ns8483/MAE156A_RobotAssistantCardiologist/Data/LinTrans.png

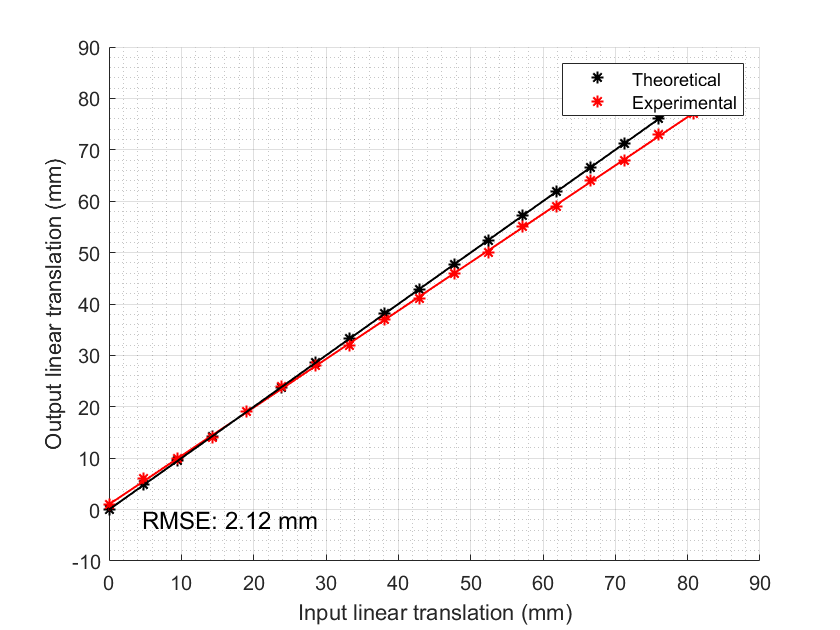
Data/LinTrans.png
