ns8483/MAE156A_RobotAssistantCardiologist/Data/Rot.png

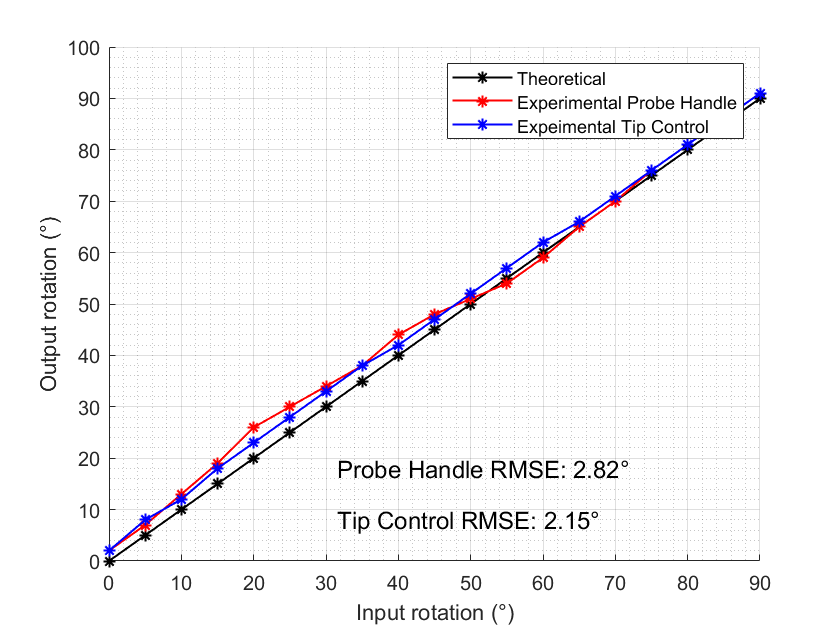
Data/Rot.png
