ns8483/MAE156A_RobotAssistantCardiologist/Images/Code Example.png

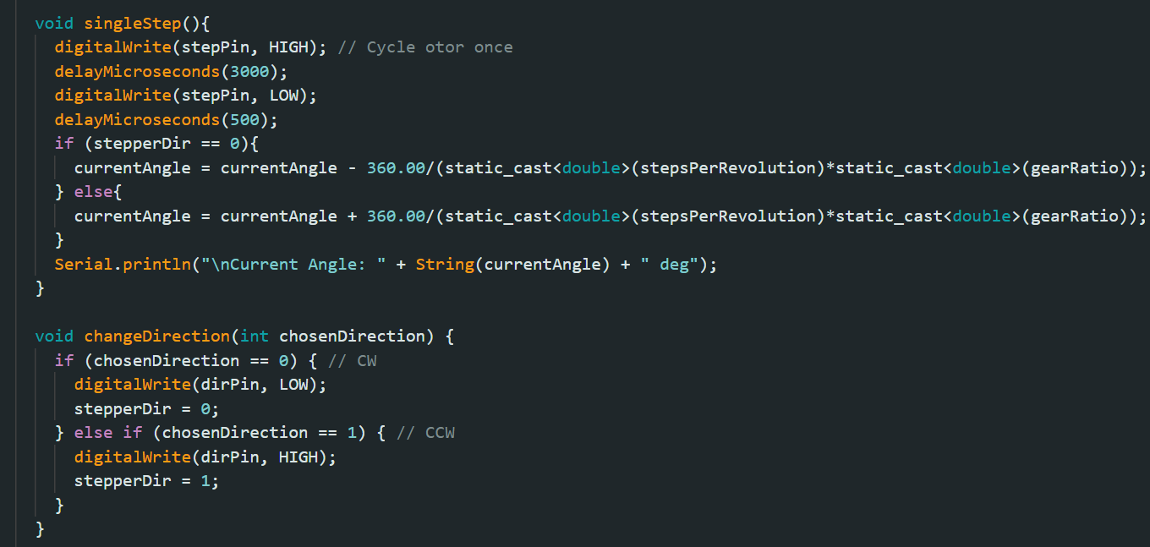
Images/Code Example.png
