ns8483/MAE156A_RobotAssistantCardiologist/Images/probe Image.png

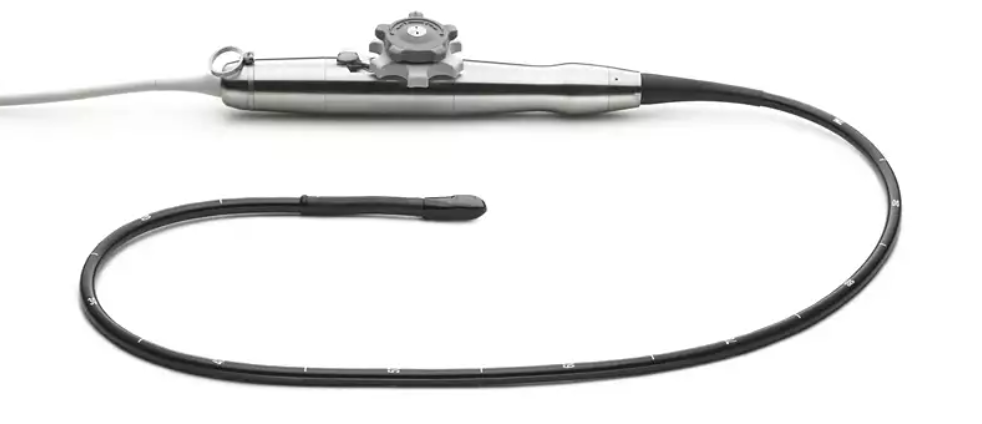
Images/probe Image.png
