ns8483/MAE156A_RobotAssistantCardiologist/Images/probe_housing.png

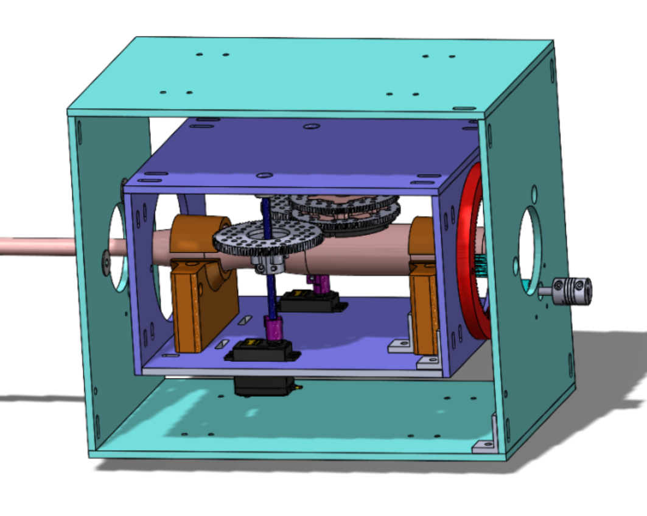
Images/probe_housing.png
