ns8483/MAE156A_RobotAssistantCardiologist/CAD/knob engagement, motorized rotation, passive translation/Inner Bearing Mount.SLDPRT

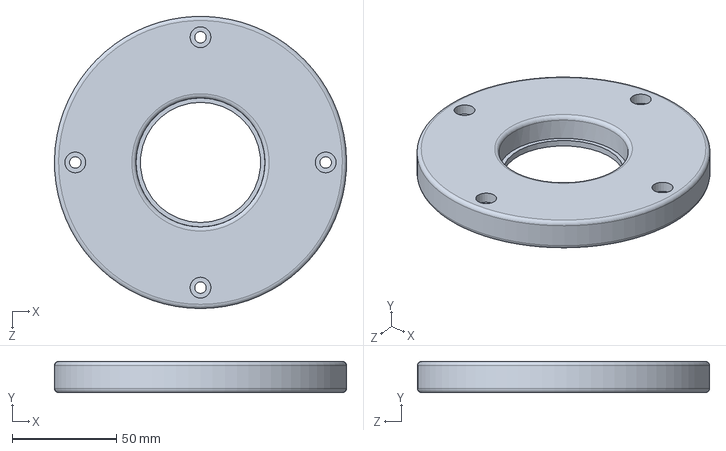
[picture p29: CAD file, 2024-04-29]
CAD/knob engagement, motorized rotation, passive translation/Inner Bearing Mount.SLDPRT
140.0 x 15.0 x 139.9 mm
