ns8483/MAE156A_RobotAssistantCardiologist/CAD/Probe and Housing/Hinge 2.SLDPRT

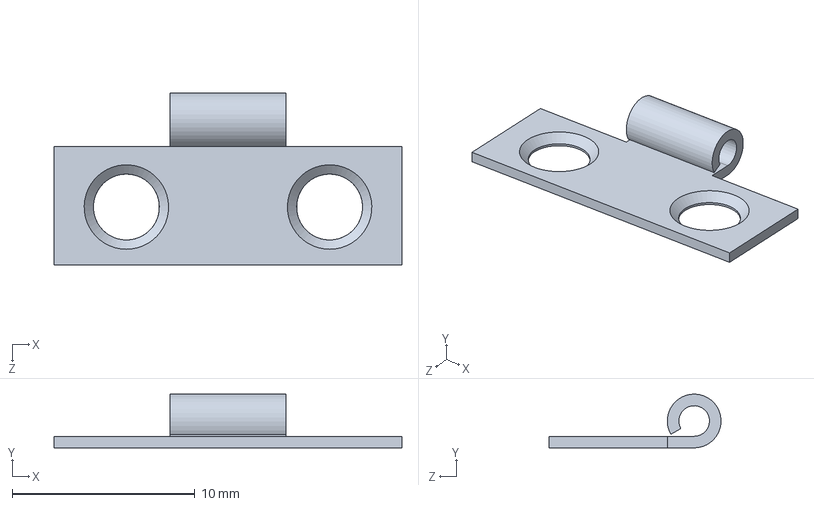
[picture p30: CAD file, 2024-04-26]
CAD/Probe and Housing/Hinge 2.SLDPRT
19.1 x 2.95 x 9.42 mm
