ns8483/MAE156A_RobotAssistantCardiologist/CAD/Base/Side.SLDPRT

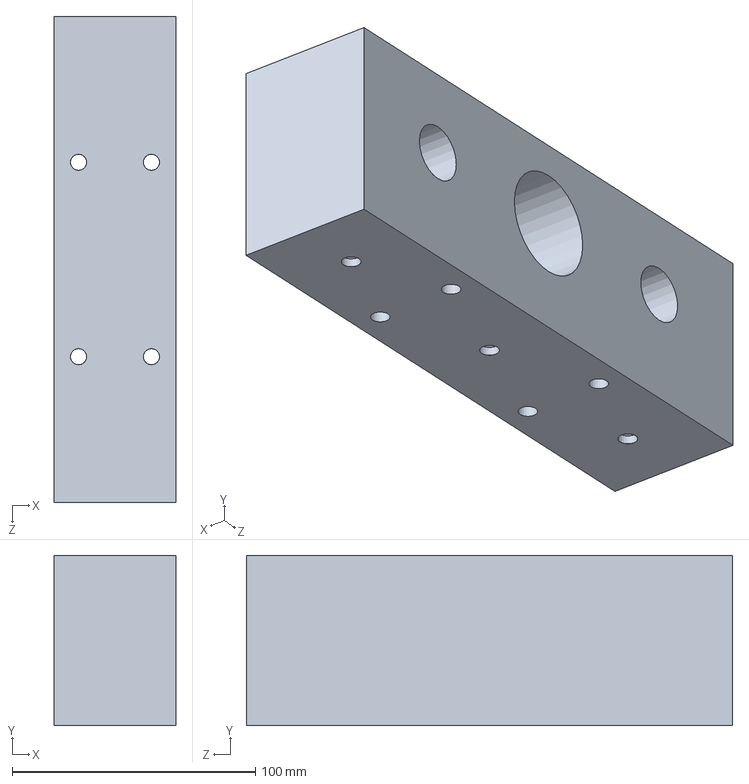
[picture p31: CAD file, 2024-04-26]
CAD/Base/Side.SLDPRT
50.0 x 70.0 x 200.0 mm
