ns8483/MAE156A_RobotAssistantCardiologist/CAD/Electronics/Controller Lid.SLDPRT

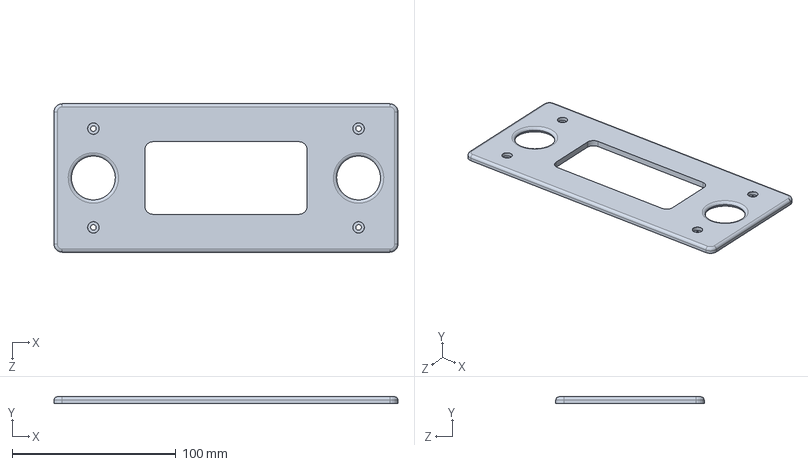
[picture p32: CAD file, 2024-05-14]
CAD/Electronics/Controller Lid.SLDPRT
210.3 x 4.00 x 90.8 mm
