ns8483/MAE156A_RobotAssistantCardiologist/CAD/Probe and Housing/big_knob_cap.SLDPRT

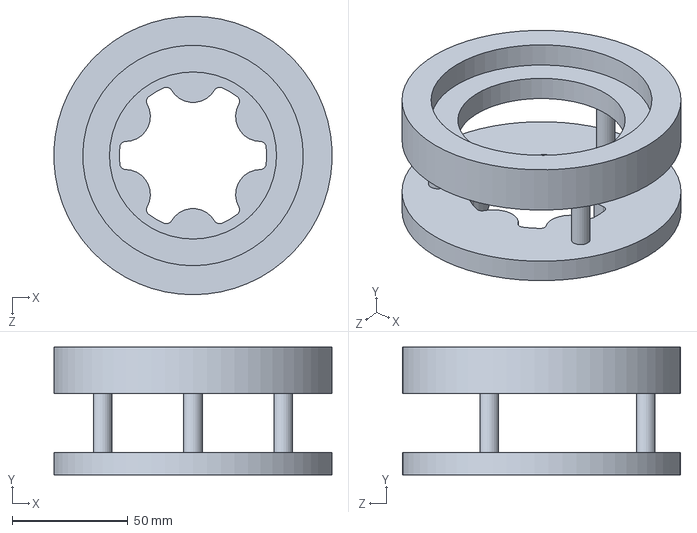
[picture p33: CAD file, 2024-04-26]
CAD/Probe and Housing/big_knob_cap.SLDPRT
119.8 x 55.1 x 120.0 mm
