ns8483/MAE156A_RobotAssistantCardiologist/CAD/Attachement/Lock Lid with Hole.SLDPRT

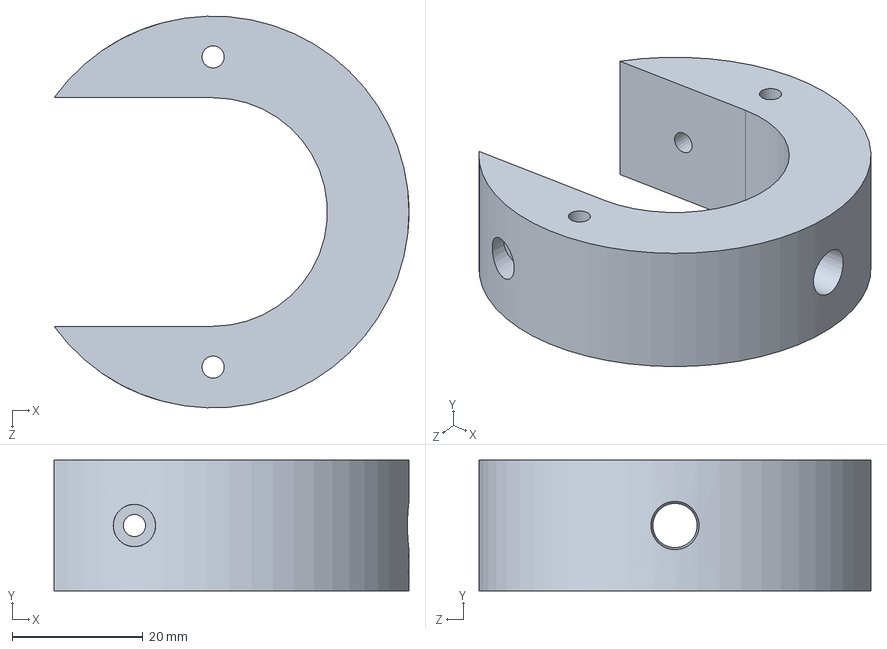
[picture p34: CAD file, 2024-05-06]
CAD/Attachement/Lock Lid with Hole.SLDPRT
54.4 x 20.0 x 60.0 mm
