ns8483/MAE156A_RobotAssistantCardiologist/CAD/Electronics/Controller Back.SLDPRT

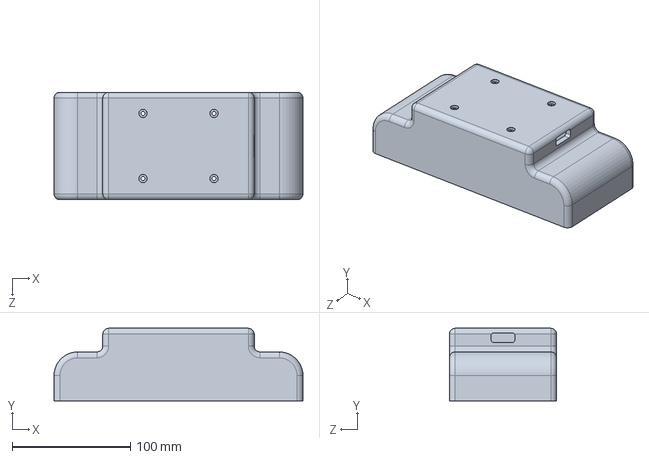
[picture p35: CAD file, 2024-05-14]
CAD/Electronics/Controller Back.SLDPRT
210.3 x 61.2 x 90.8 mm
