ns8483/MAE156A_RobotAssistantCardiologist/CAD/knob engagement, motorized rotation, passive translation/Outer Bearing Mount.SLDPRT

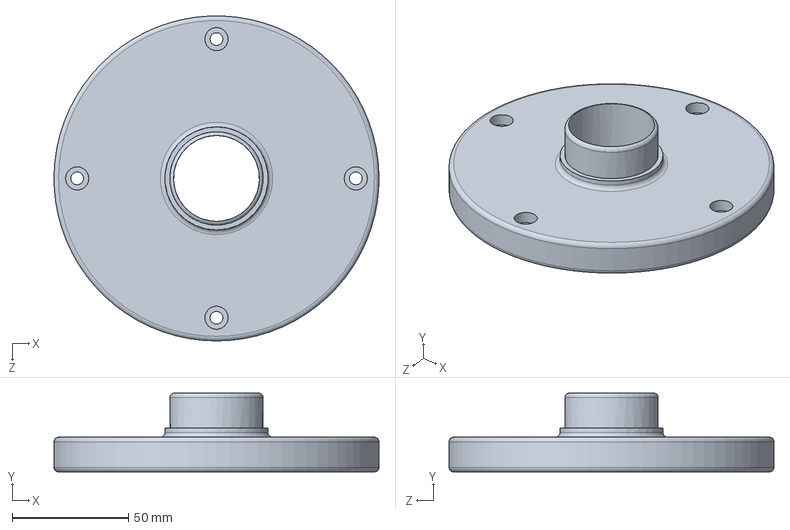
[picture p36: CAD file, 2024-04-29]
CAD/knob engagement, motorized rotation, passive translation/Outer Bearing Mount.SLDPRT
140.0 x 34.0 x 139.9 mm
