ns8483/MAE156A_RobotAssistantCardiologist/CAD/Probe and Housing/small_knob.SLDPRT

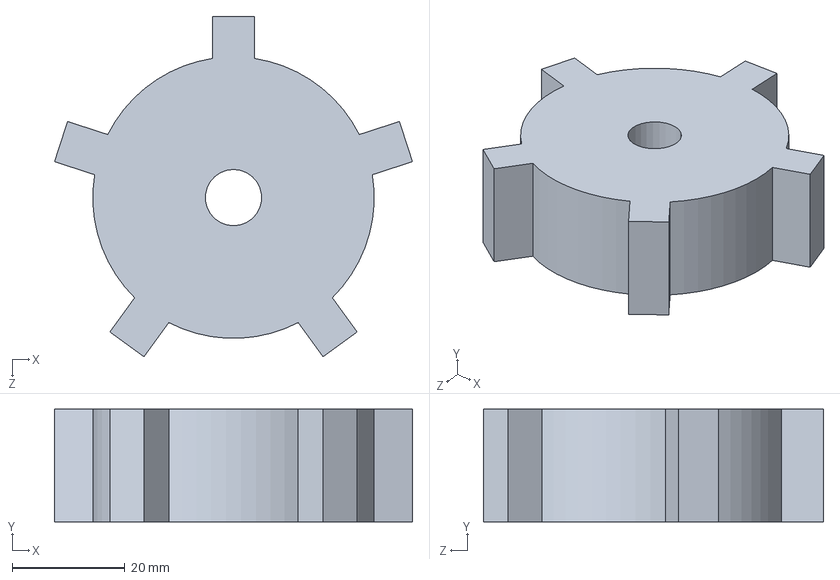
[picture p37: CAD file, 2024-04-26]
CAD/Probe and Housing/small_knob.SLDPRT
63.6 x 20.0 x 60.5 mm
