ns8483/MAE156A_RobotAssistantCardiologist/CAD/Base/Bed Adapter.SLDPRT

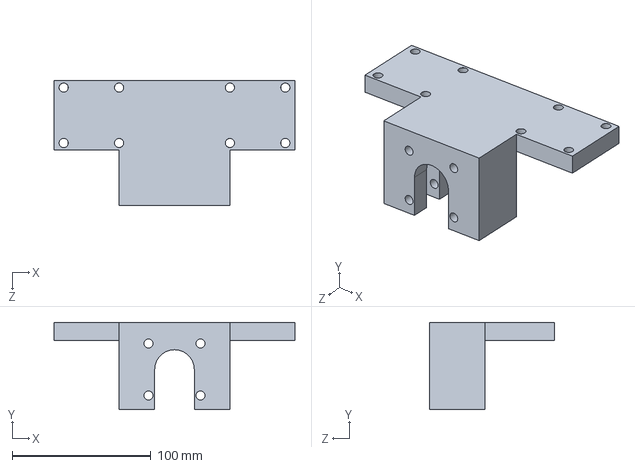
[picture p38: CAD file, 2024-04-26]
CAD/Base/Bed Adapter.SLDPRT
174.0 x 63.0 x 90.0 mm
