ns8483/MAE156A_RobotAssistantCardiologist/CAD/Electronics/Controller Front.SLDPRT

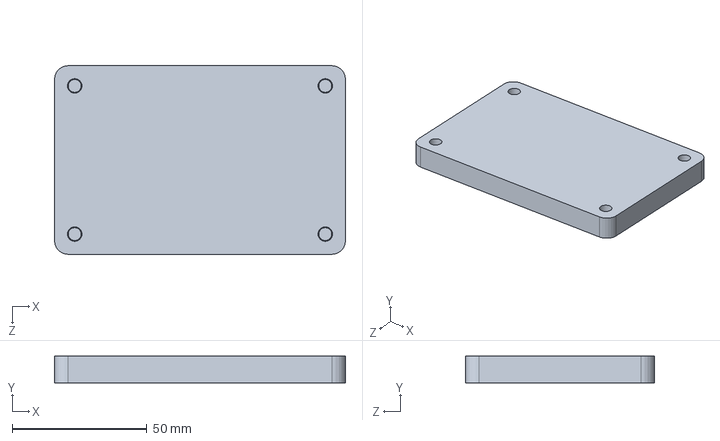
[picture p39: CAD file, 2024-05-08]
CAD/Electronics/Controller Front.SLDPRT
108.0 x 10.0 x 70.0 mm
