ns8483/MAE156A_RobotAssistantCardiologist/CAD/Probe and Housing/NeedleBearing_PartNumberNTB100135.SLDPRT

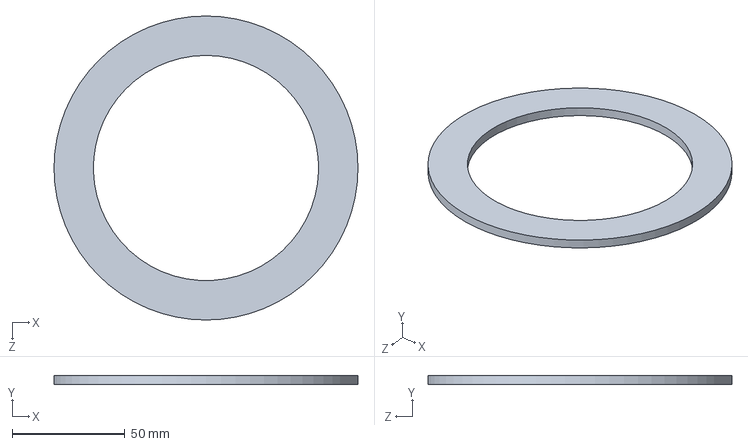
[picture p40: CAD file, 2024-04-26]
CAD/Probe and Housing/NeedleBearing_PartNumberNTB100135.SLDPRT
135.0 x 4.00 x 135.0 mm
