ns8483/MAE156A_RobotAssistantCardiologist/CAD/Arm V2/T-Slotted Framing (150mm L).SLDPRT

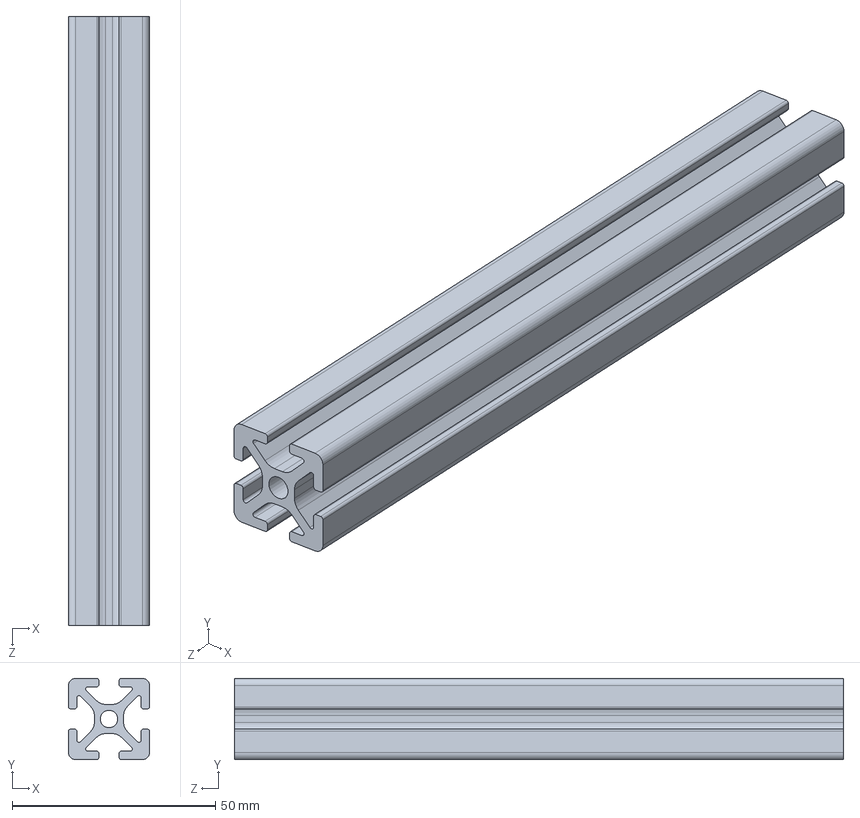
[picture p41: CAD file, 2024-05-30]
CAD/Arm V2/T-Slotted Framing (150mm L).SLDPRT
20.0 x 20.0 x 150.0 mm
