ns8483/MAE156A_RobotAssistantCardiologist/CAD/Attachement/10mm OD 400mm L.SLDPRT

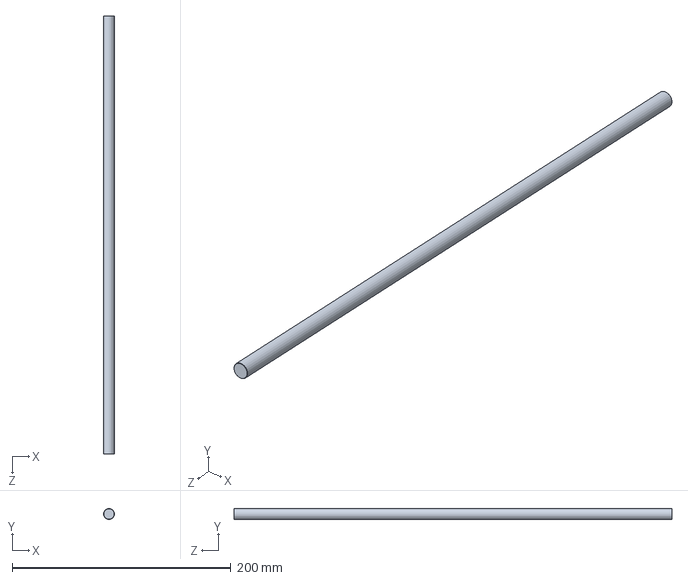
[picture p42: CAD file, 2024-04-26]
CAD/Attachement/10mm OD 400mm L.SLDPRT
10.0 x 10.0 x 400.0 mm
