ns8483/MAE156A_RobotAssistantCardiologist/CAD/Base/10mm ID.SLDPRT

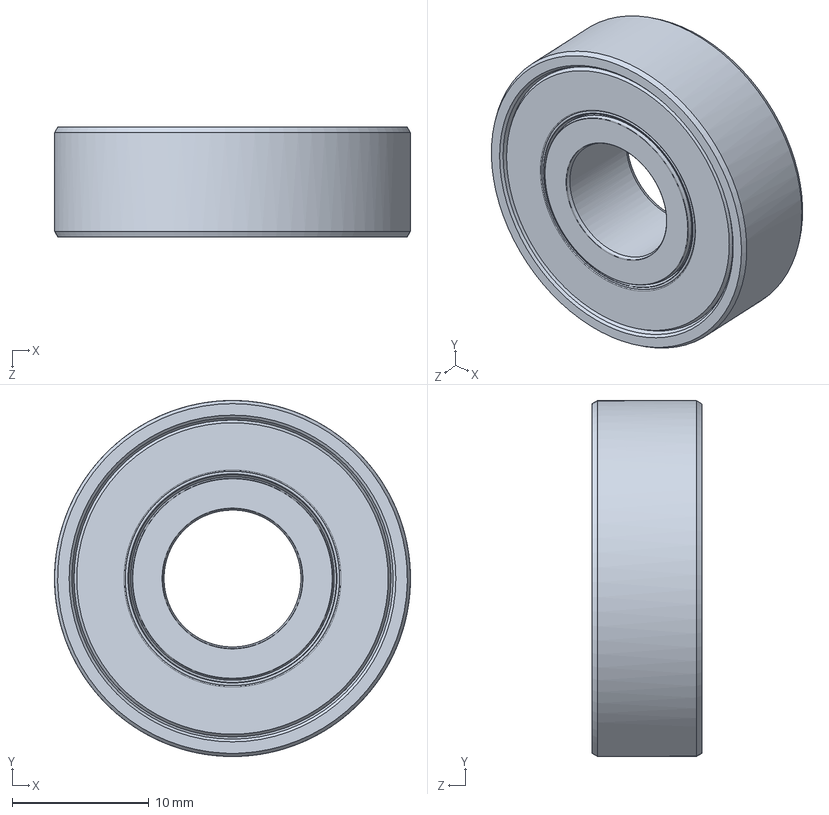
[picture p43: CAD file, 2024-04-26]
CAD/Base/10mm ID.SLDPRT
26.0 x 26.0 x 8.00 mm
