ns8483/MAE156A_RobotAssistantCardiologist/CAD/Electronics/Cable Box (female).SLDPRT

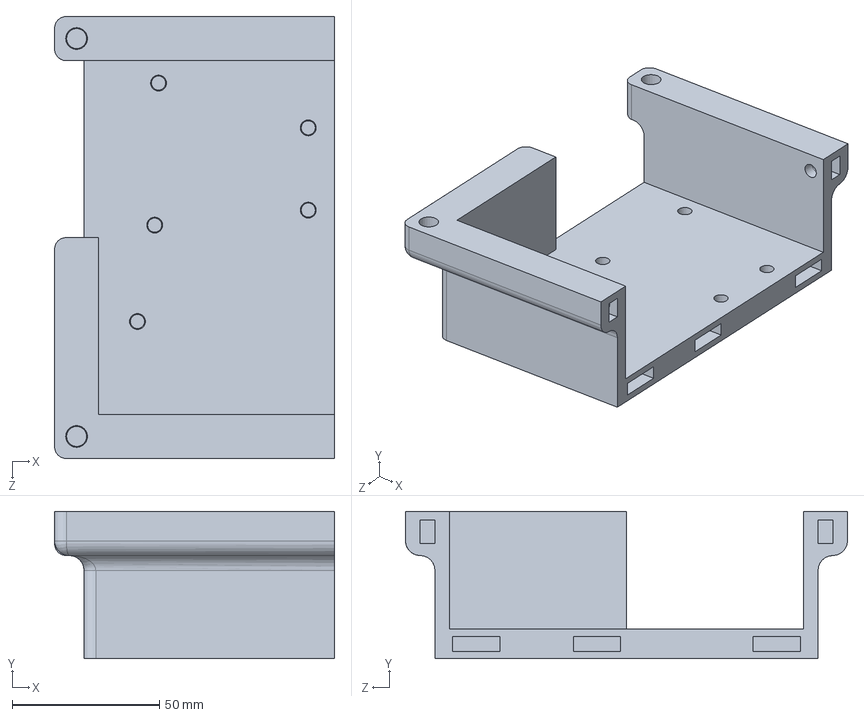
[picture p44: CAD file, 2024-05-06]
CAD/Electronics/Cable Box (female).SLDPRT
95.0 x 50.0 x 150.0 mm
