ns8483/MAE156A_RobotAssistantCardiologist/CAD/knob engagement, motorized rotation, passive translation/2302-0032-0100.SLDPRT

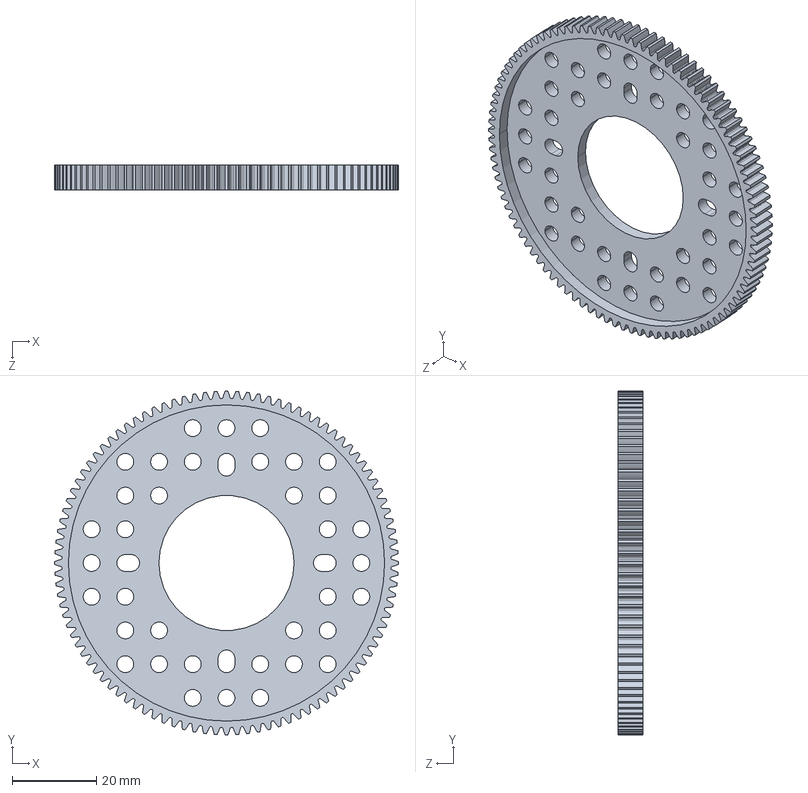
[picture p45: CAD file, 2024-04-28]
CAD/knob engagement, motorized rotation, passive translation/2302-0032-0100.SLDPRT
81.6 x 81.6 x 6.00 mm
