ns8483/MAE156A_RobotAssistantCardiologist/CAD/Probe and Housing/Holder.SLDPRT

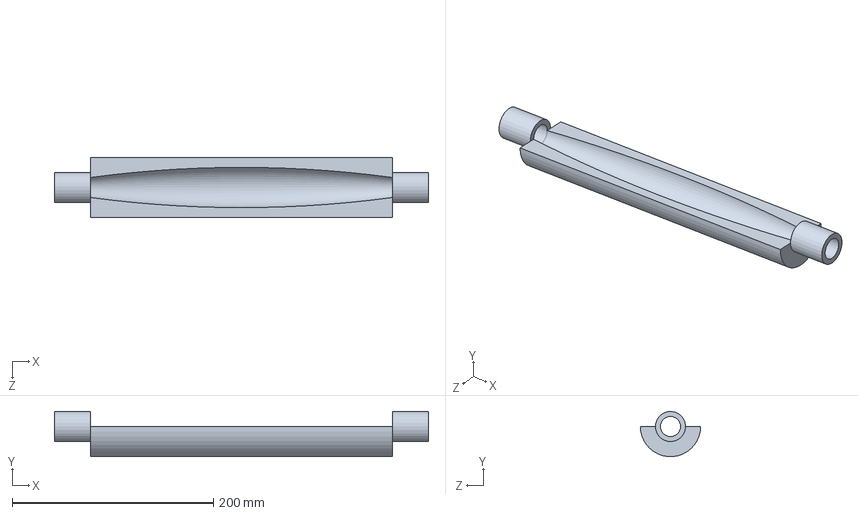
[picture p46: CAD file, 2024-04-26]
CAD/Probe and Housing/Holder.SLDPRT
372.0 x 44.9 x 60.0 mm
