ns8483/MAE156A_RobotAssistantCardiologist/CAD/Attachement/Square Lock pin.SLDPRT

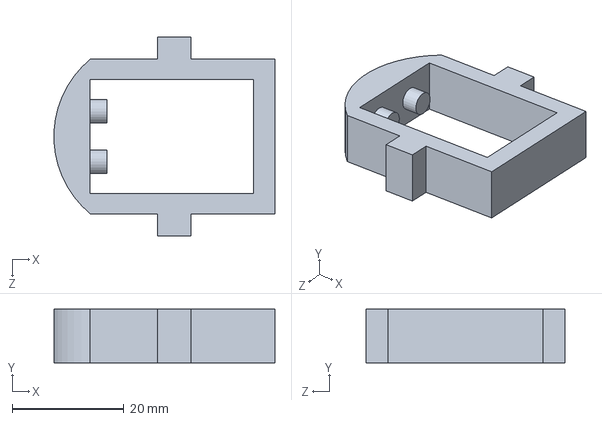
[picture p47: CAD file, 2024-04-26]
CAD/Attachement/Square Lock pin.SLDPRT
39.5 x 9.60 x 35.6 mm
