ns8483/MAE156A_RobotAssistantCardiologist/CAD/Base/Bracket.SLDPRT

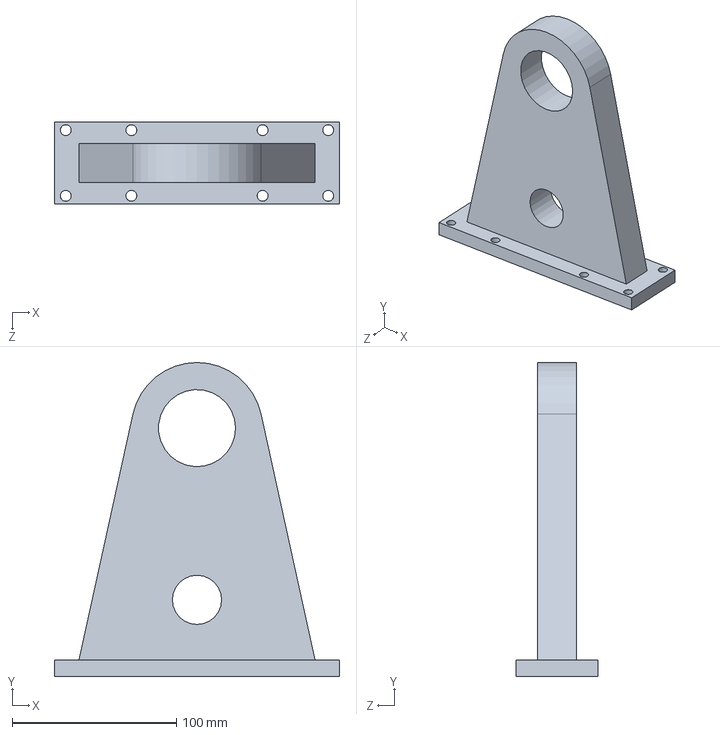
[picture p48: CAD file, 2024-04-26]
CAD/Base/Bracket.SLDPRT
174.0 x 191.4 x 50.0 mm
