ns8483/MAE156A_RobotAssistantCardiologist/CAD/Electronics/Cable Box.SLDPRT

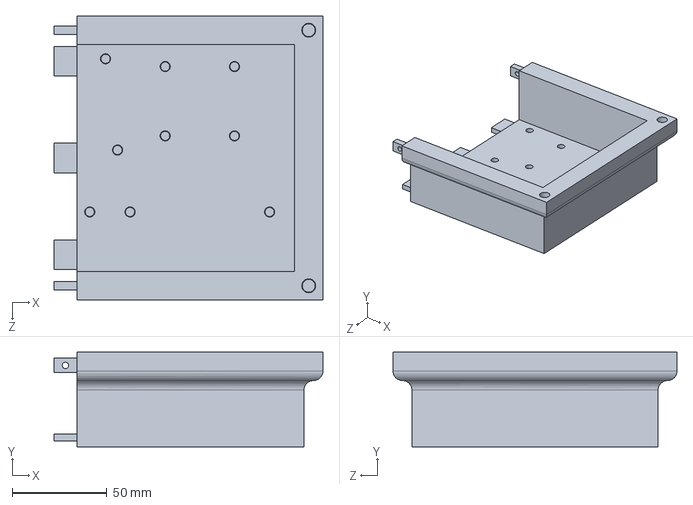
[picture p49: CAD file, 2024-05-06]
CAD/Electronics/Cable Box.SLDPRT
142.0 x 50.0 x 150.0 mm
