ns8483/MAE156A_RobotAssistantCardiologist/CAD/knob engagement, motorized rotation, passive translation/end acrylic 2.SLDPRT

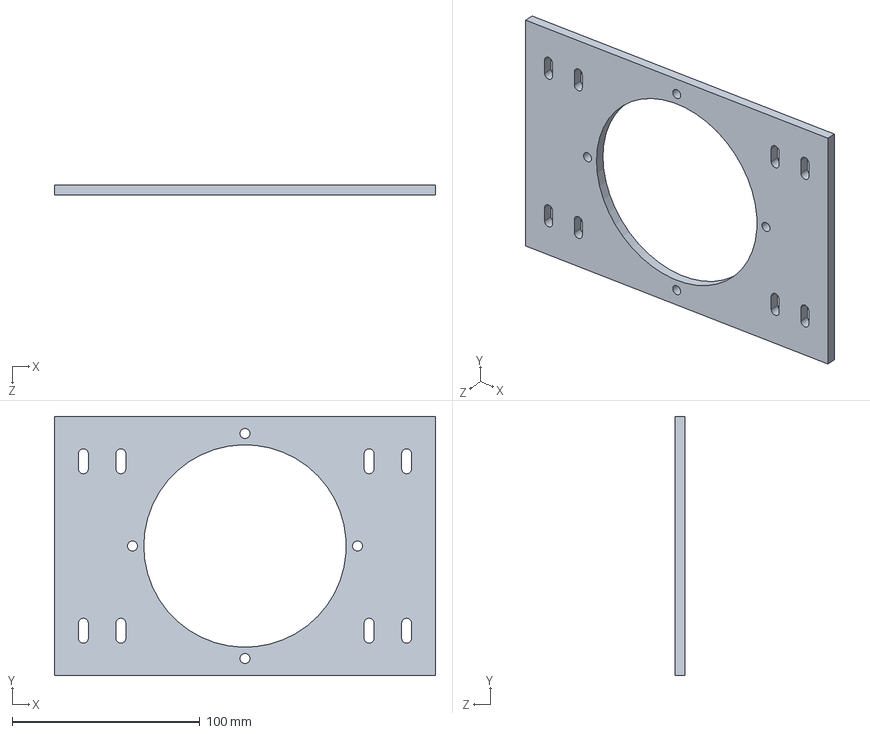
[picture p50: CAD file, 2024-04-28]
CAD/knob engagement, motorized rotation, passive translation/end acrylic 2.SLDPRT
203.2 x 138.2 x 5.59 mm
