ns8483/MAE156A_RobotAssistantCardiologist/CAD/Probe and Housing/NeedleBearing_PartNumberNTB7095.SLDPRT

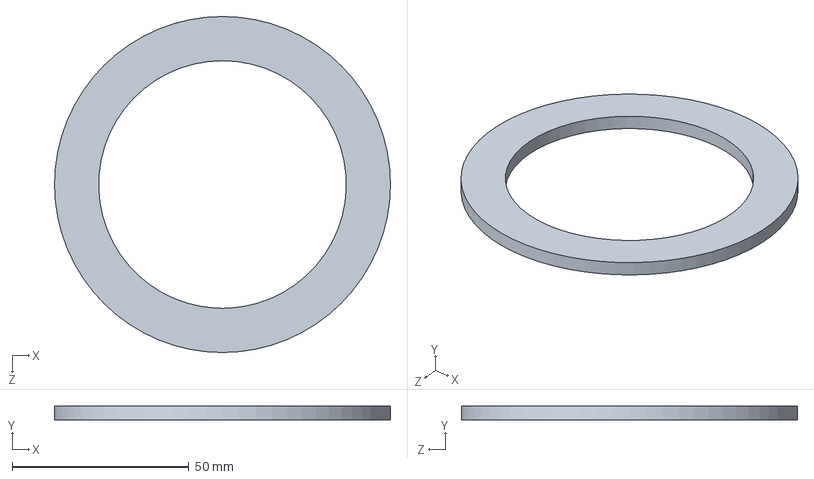
[picture p51: CAD file, 2024-04-26]
CAD/Probe and Housing/NeedleBearing_PartNumberNTB7095.SLDPRT
95.0 x 4.00 x 95.0 mm
