ns8483/MAE156A_RobotAssistantCardiologist/CAD/Attachement/Base Plate Other Side.SLDPRT

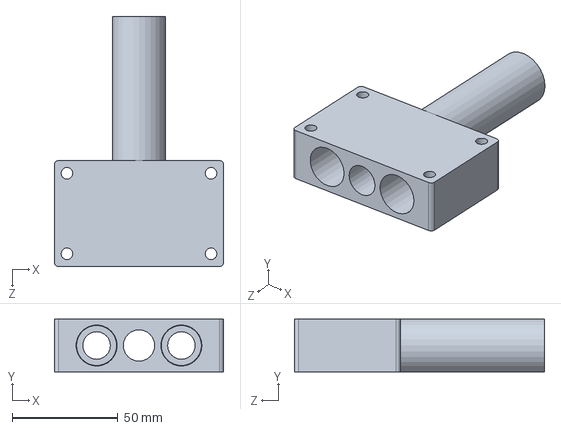
[picture p52: CAD file, 2024-04-26]
CAD/Attachement/Base Plate Other Side.SLDPRT
80.0 x 25.0 x 118.0 mm
