ns8483/MAE156A_RobotAssistantCardiologist/CAD/knob engagement, motorized rotation, passive translation/New Probe.SLDPRT

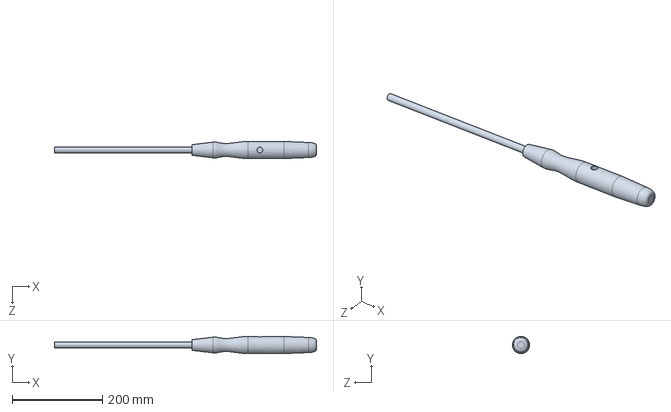
[picture p53: CAD file, 2024-04-28]
CAD/knob engagement, motorized rotation, passive translation/New Probe.SLDPRT
579.8 x 38.1 x 38.1 mm
