ns8483/MAE156A_RobotAssistantCardiologist/CAD/Attachement/Square Lid.SLDPRT

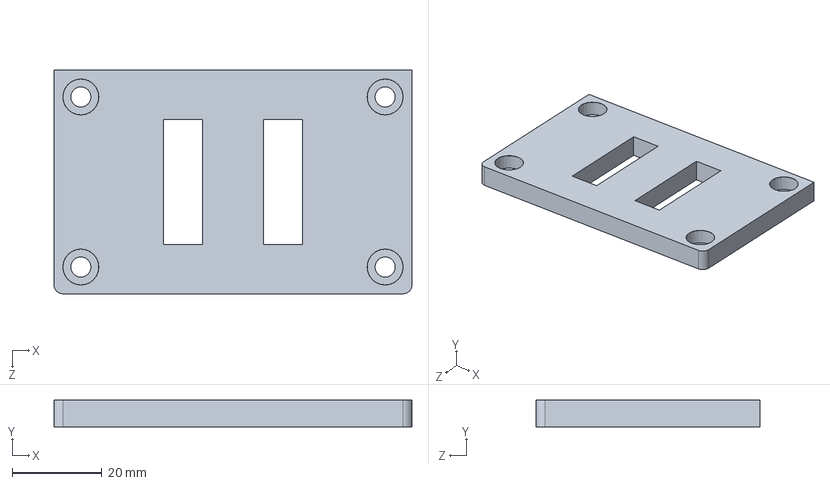
[picture p54: CAD file, 2024-04-26]
CAD/Attachement/Square Lid.SLDPRT
80.0 x 6.00 x 50.0 mm
