ns8483/MAE156A_RobotAssistantCardiologist/CAD/Electronics/Cable Box Lid.SLDPRT

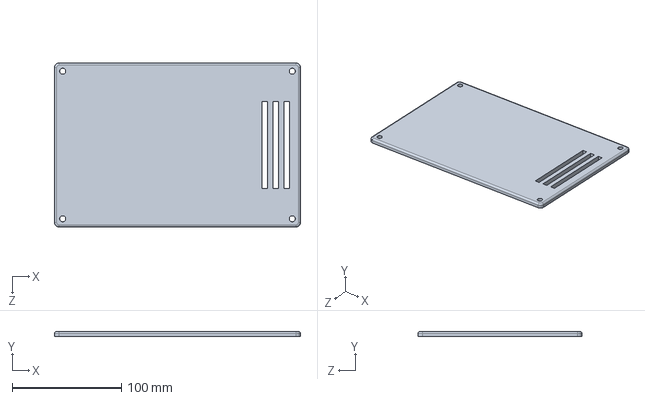
[picture p55: CAD file, 2024-05-06]
CAD/Electronics/Cable Box Lid.SLDPRT
225.0 x 5.00 x 150.0 mm
