ns8483/MAE156A_RobotAssistantCardiologist/CAD/knob engagement, motorized rotation, passive translation/2101-0006-0060.STEP

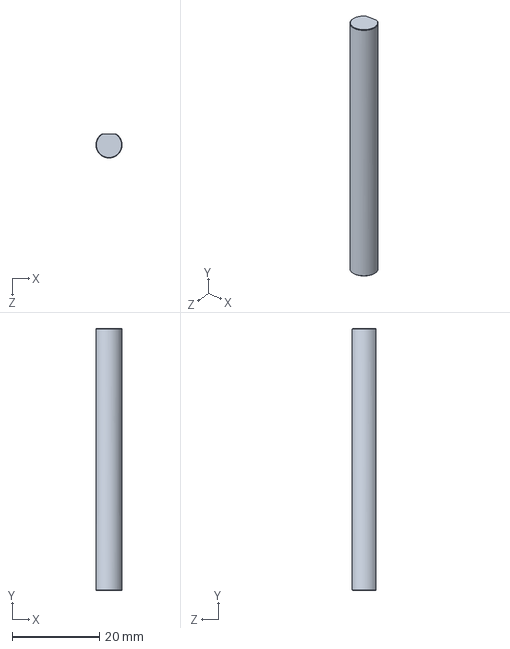
[picture p56: CAD file, 2024-04-28]
CAD/knob engagement, motorized rotation, passive translation/2101-0006-0060.STEP
6.00 x 60.0 x 5.50 mm
