ns8483/MAE156A_RobotAssistantCardiologist/CAD/Probe and Housing/am-2964a Neverest Classic 40.STEP

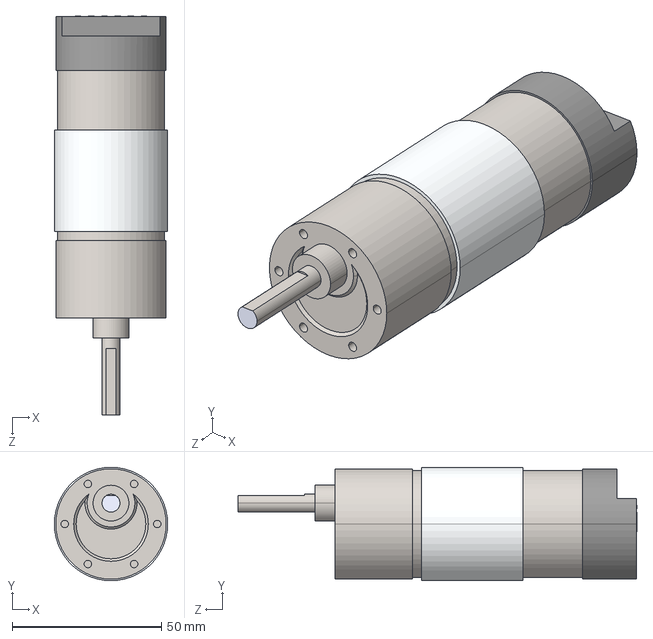
[picture p57: CAD file, 2024-04-26]
CAD/Probe and Housing/am-2964a Neverest Classic 40.STEP
38.0 x 38.0 x 133.7 mm
