ns8483/MAE156A_RobotAssistantCardiologist/CAD/Base/Base.SLDPRT

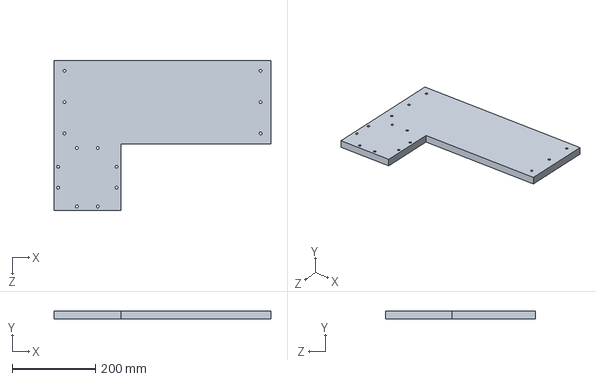
[picture p58: CAD file, 2024-04-26]
CAD/Base/Base.SLDPRT
520.0 x 20.0 x 360.0 mm
