ns8483/MAE156A_RobotAssistantCardiologist/CAD/knob engagement, motorized rotation, passive translation/2500-0010-0240.step

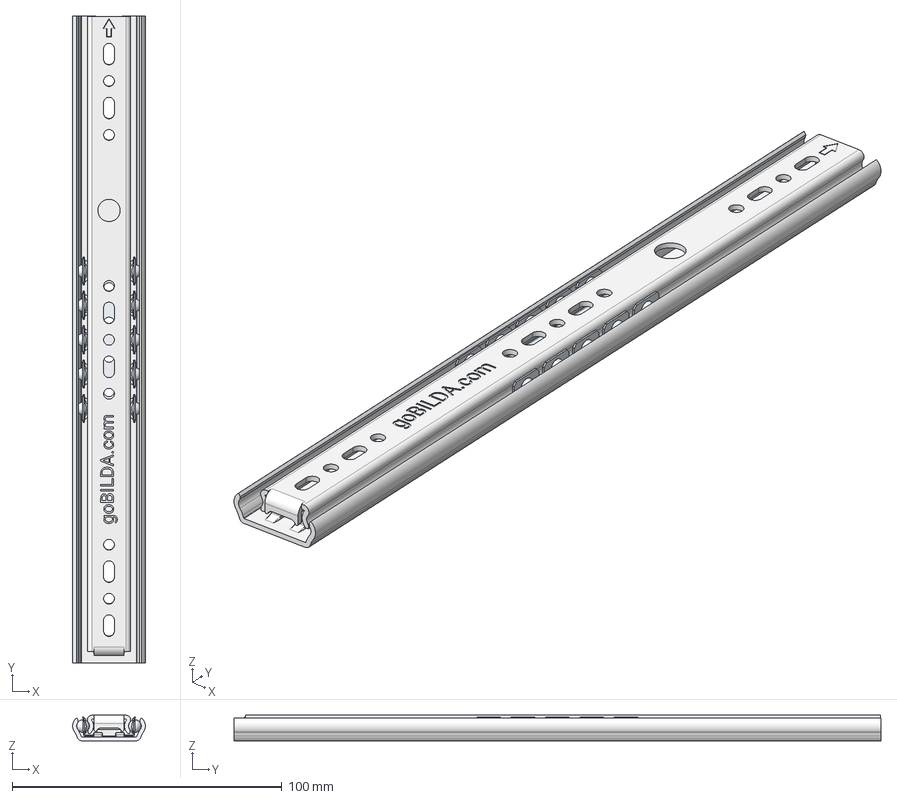
[picture p59: CAD file, 2024-04-28]
CAD/knob engagement, motorized rotation, passive translation/2500-0010-0240.step
27.0 x 240.0 x 9.50 mm
In
Out
Ball x 10
