ns8483/MAE156A_RobotAssistantCardiologist/CAD/Probe and Housing/New Probe.SLDPRT

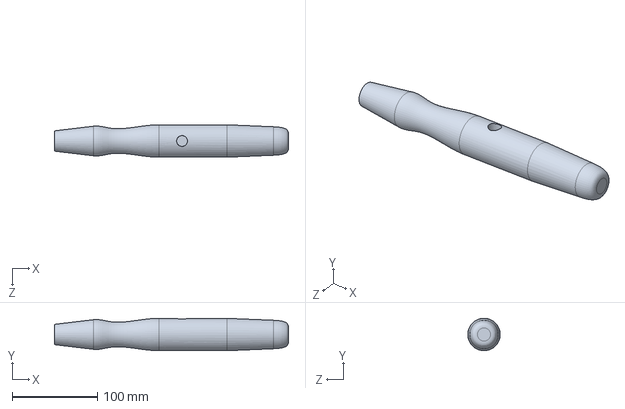
[picture p60: CAD file, 2024-04-26]
CAD/Probe and Housing/New Probe.SLDPRT
275.0 x 38.1 x 38.1 mm
