ns8483/MAE156A_RobotAssistantCardiologist/CAD/Attachement/Lock Internal Block.SLDPRT

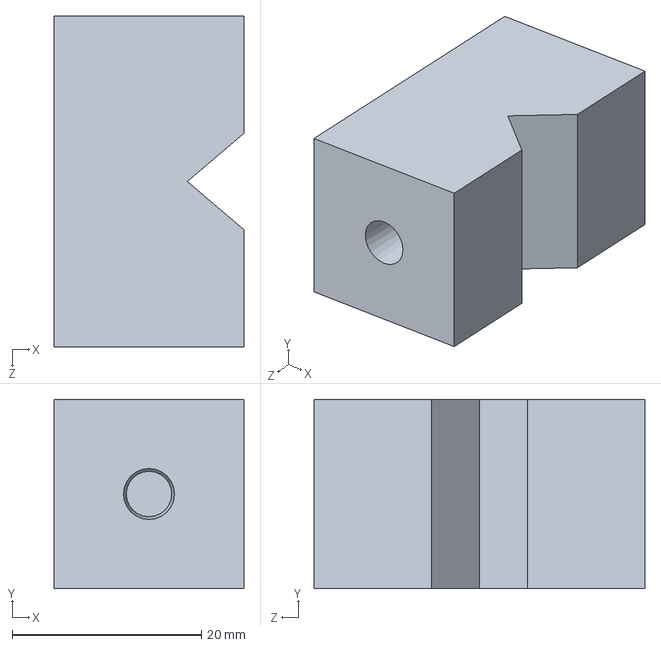
[picture p61: CAD file, 2024-04-26]
CAD/Attachement/Lock Internal Block.SLDPRT
20.1 x 20.0 x 35.0 mm
