ns8483/MAE156A_RobotAssistantCardiologist/CAD/Base/Catheter Guide Block.SLDPRT

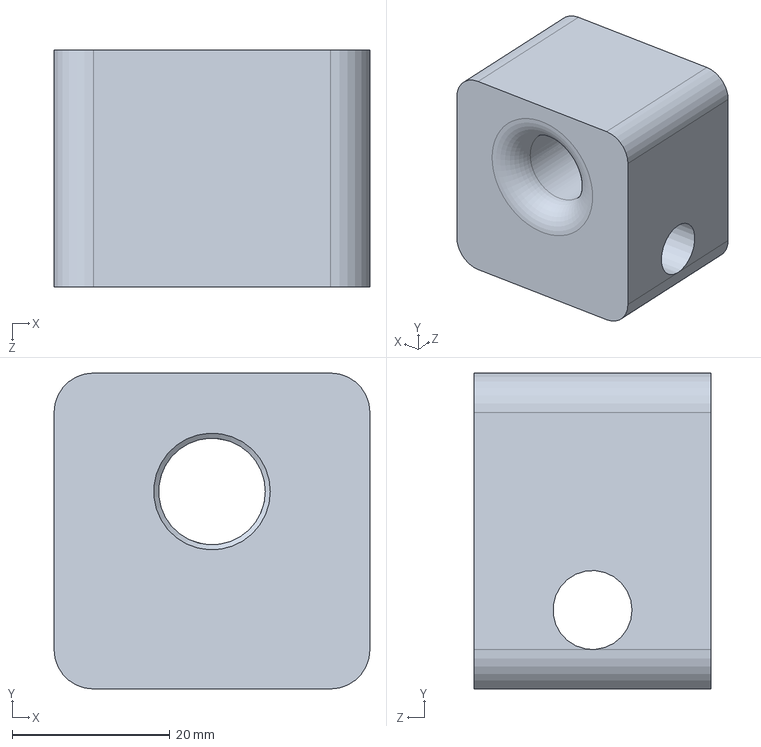
[picture p62: CAD file, 2024-04-26]
CAD/Base/Catheter Guide Block.SLDPRT
40.0 x 40.0 x 30.0 mm
