ns8483/MAE156A_RobotAssistantCardiologist/CAD/Electronics/arduino mega case_bottom.step

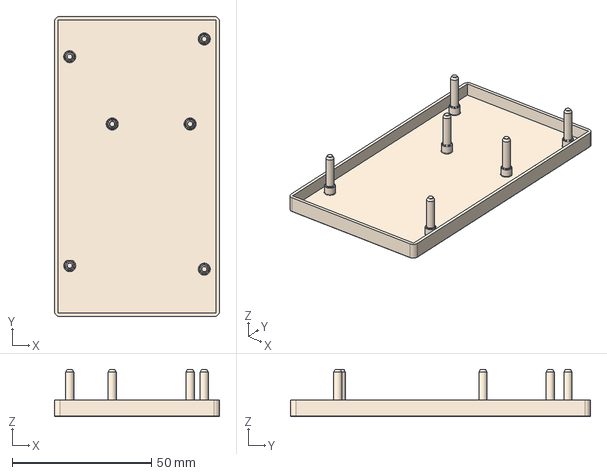
[picture p63: CAD file, 2024-04-29]
CAD/Electronics/arduino mega case_bottom.step
59.3 x 107.6 x 16.9 mm
