ns8483/MAE156A_RobotAssistantCardiologist/CAD/Attachement/Lock Base.SLDPRT

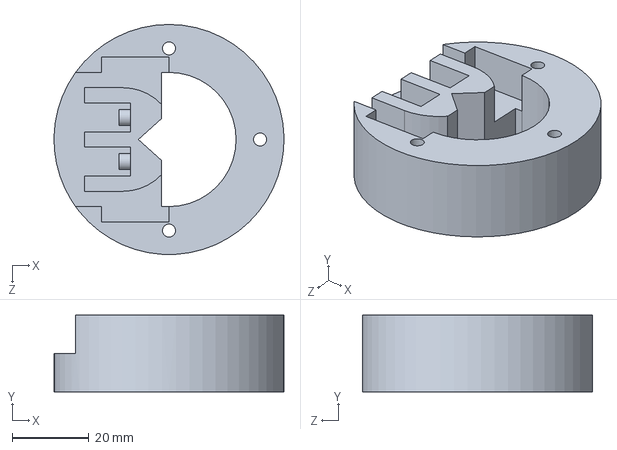
[picture p65: CAD file, 2024-04-26]
CAD/Attachement/Lock Base.SLDPRT
60.0 x 20.0 x 60.0 mm
