ns8483/MAE156A_RobotAssistantCardiologist/CAD/Electronics/arduino mega case_top.step

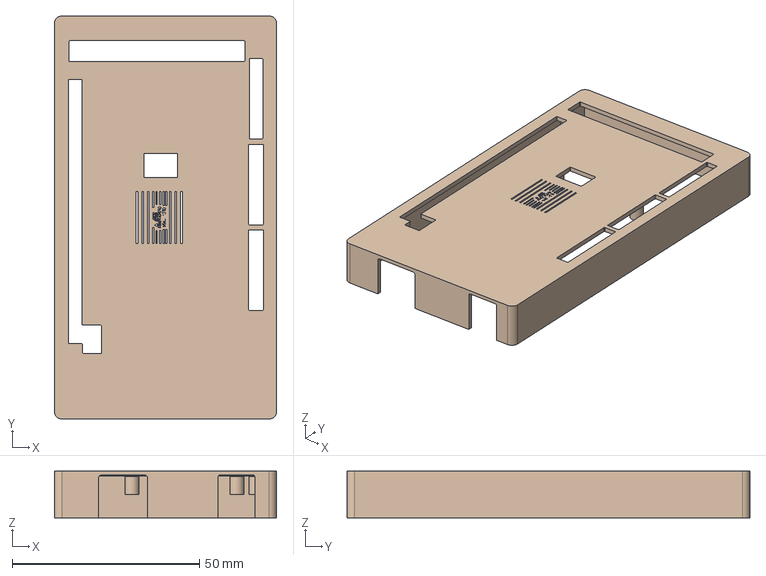
[picture p66: CAD file, 2024-04-29]
CAD/Electronics/arduino mega case_top.step
59.3 x 107.6 x 12.5 mm
