ns8483/MAE156A_RobotAssistantCardiologist/CAD/Probe and Housing/lid.SLDPRT

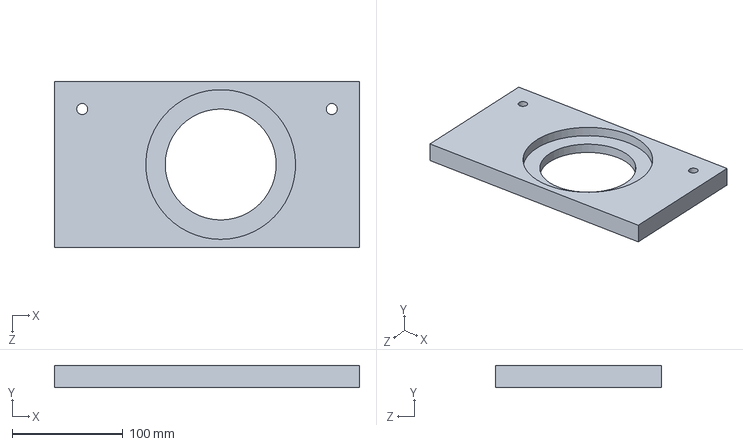
[picture p67: CAD file, 2024-04-26]
CAD/Probe and Housing/lid.SLDPRT
275.0 x 20.0 x 150.0 mm
