ns8483/MAE156A_RobotAssistantCardiologist/CAD/Attachement/square lock base.SLDPRT

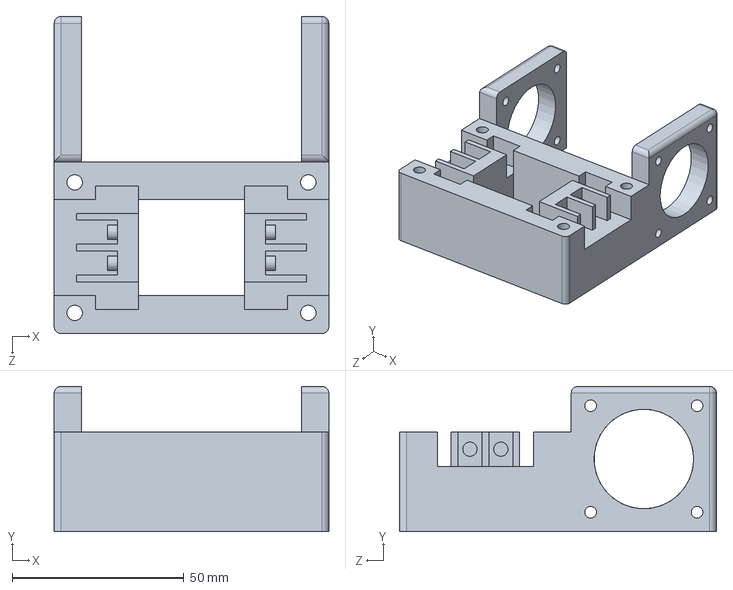
[picture p68: CAD file, 2024-04-26]
CAD/Attachement/square lock base.SLDPRT
80.0 x 42.3 x 92.3 mm
