ns8483/MAE156A_RobotAssistantCardiologist/CAD/knob engagement, motorized rotation, passive translation/Dial Large Press Fit.SLDPRT

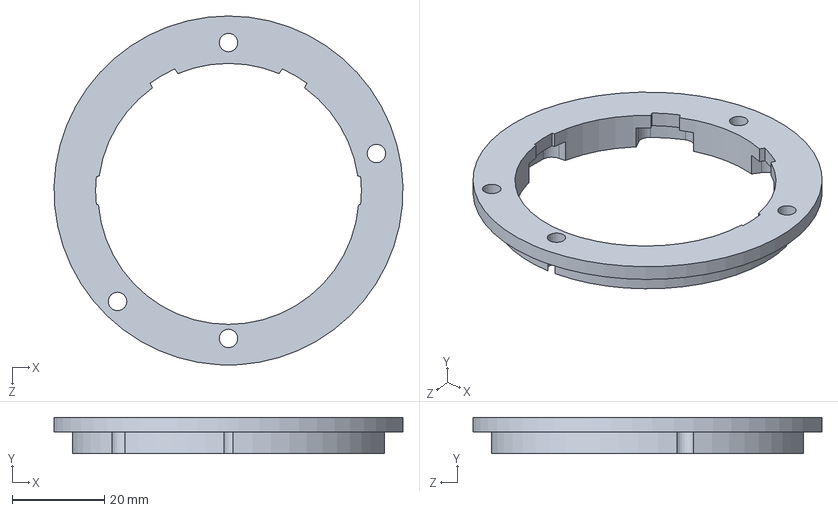
[picture p69: CAD file, 2024-04-28]
CAD/knob engagement, motorized rotation, passive translation/Dial Large Press Fit.SLDPRT
75.5 x 7.83 x 75.5 mm
