ns8483/MAE156A_RobotAssistantCardiologist/CAD/Probe and Housing/probe.SLDPRT

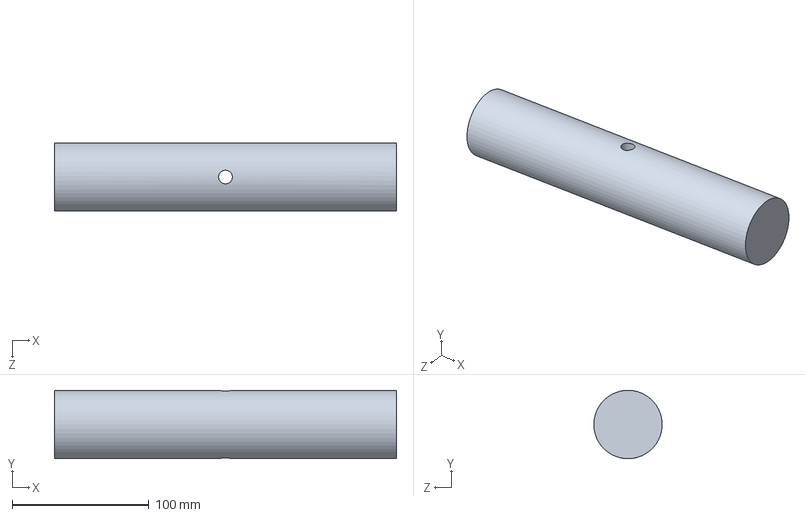
[picture p70: CAD file, 2024-04-26]
CAD/Probe and Housing/probe.SLDPRT
250.0 x 50.0 x 50.0 mm
