ns8483/MAE156A_RobotAssistantCardiologist/CAD/Attachement/Rotator Holder.SLDPRT

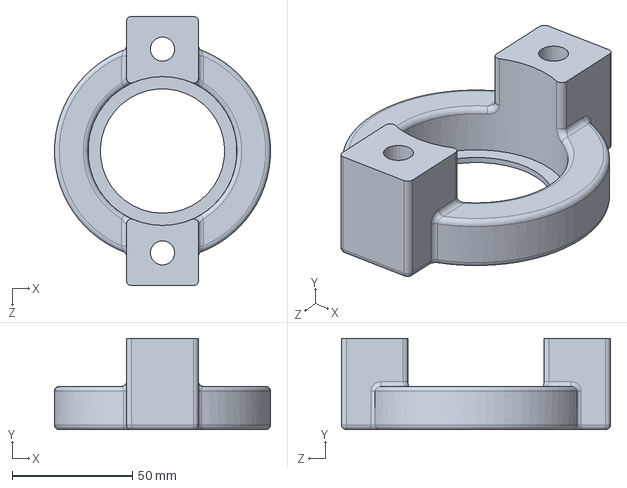
[picture p71: CAD file, 2024-04-26]
CAD/Attachement/Rotator Holder.SLDPRT
90.0 x 38.0 x 112.0 mm
