ns8483/MAE156A_RobotAssistantCardiologist/CAD/Probe and Housing/small_knob_cap.SLDPRT

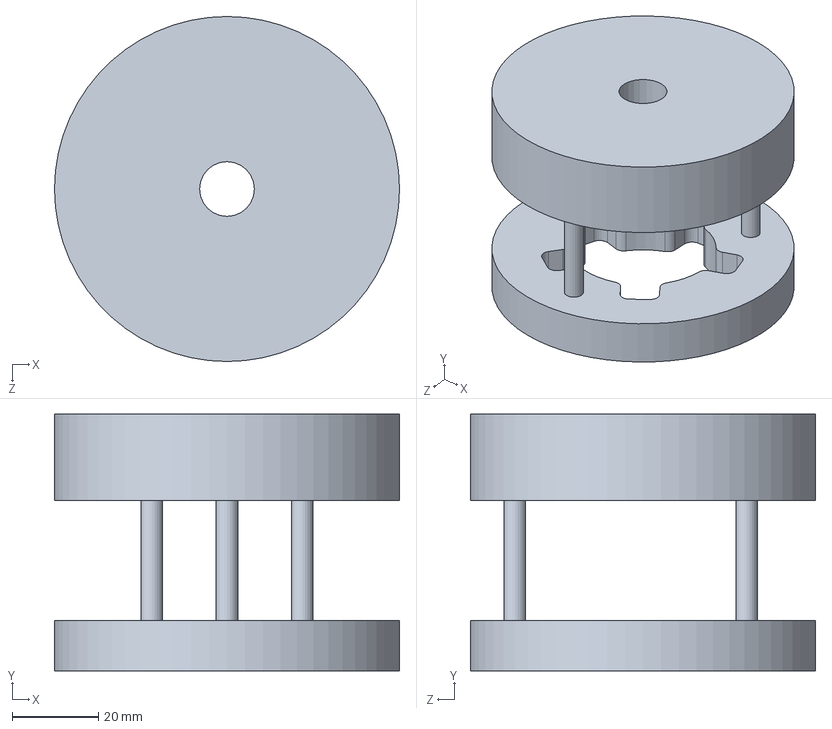
[picture p72: CAD file, 2024-04-26]
CAD/Probe and Housing/small_knob_cap.SLDPRT
80.0 x 59.6 x 80.0 mm
