ns8483/MAE156A_RobotAssistantCardiologist/CAD/Attachement/Shaft Adapter.SLDPRT

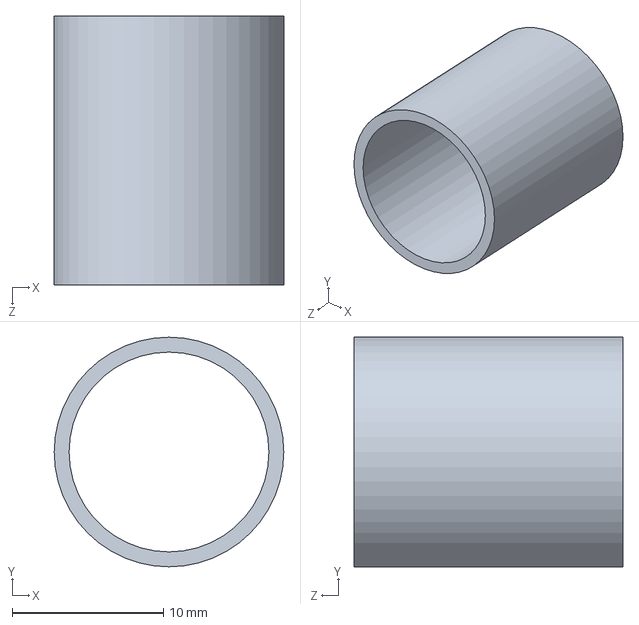
[picture p73: CAD file, 2024-04-26]
CAD/Attachement/Shaft Adapter.SLDPRT
15.2 x 15.2 x 17.8 mm
