ns8483/MAE156A_RobotAssistantCardiologist/CAD/Probe and Housing/New Probe Box.SLDPRT

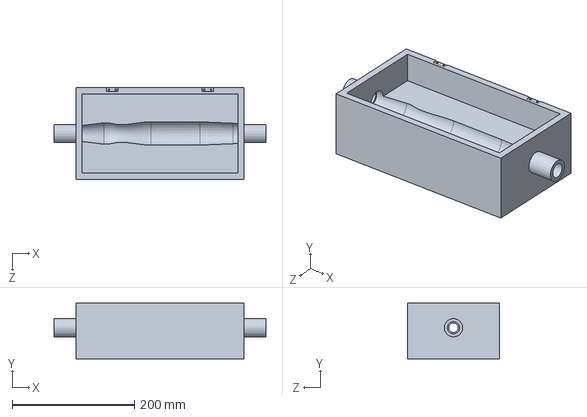
[picture p74: CAD file, 2024-04-26]
CAD/Probe and Housing/New Probe Box.SLDPRT
347.0 x 90.9 x 150.0 mm
