ns8483/MAE156A_RobotAssistantCardiologist/CAD/Attachement/Lock Pin.SLDPRT

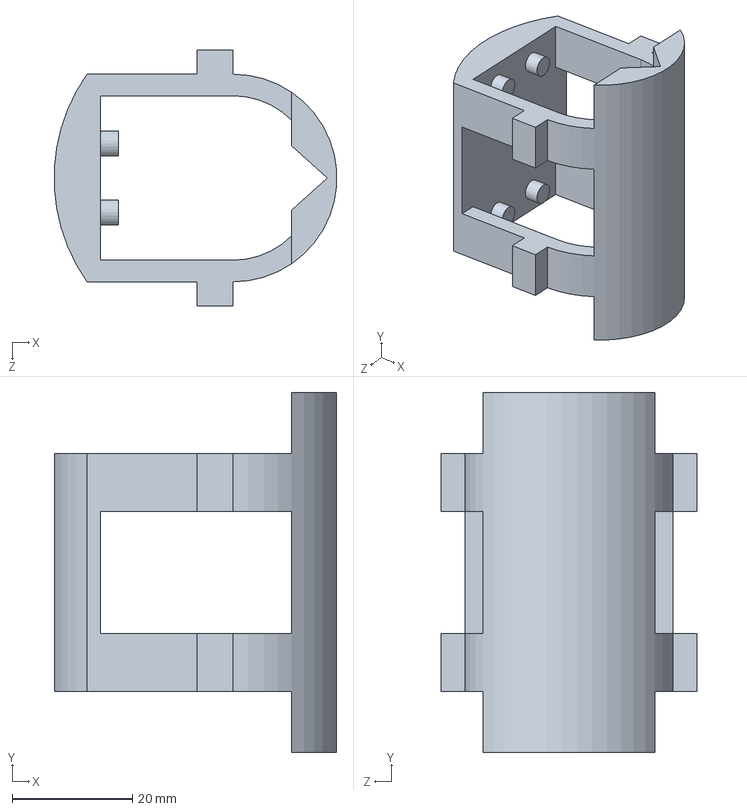
[picture p75: CAD file, 2024-04-26]
CAD/Attachement/Lock Pin.SLDPRT
47.1 x 60.0 x 42.6 mm
