ns8483/MAE156A_RobotAssistantCardiologist/CAD/Base/Bracket Roller.SLDPRT

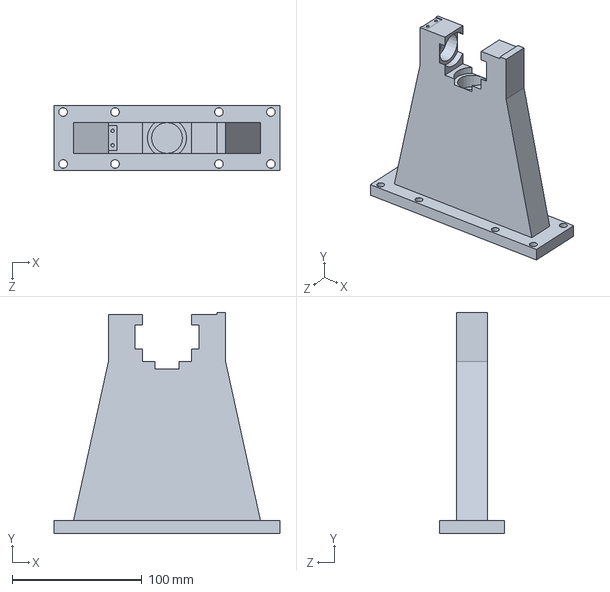
[picture p76: CAD file, 2024-04-26]
CAD/Base/Bracket Roller.SLDPRT
174.0 x 170.4 x 50.0 mm
