ns8483/MAE156A_RobotAssistantCardiologist/CAD/knob engagement, motorized rotation, passive translation/small knob shell 2.SLDPRT

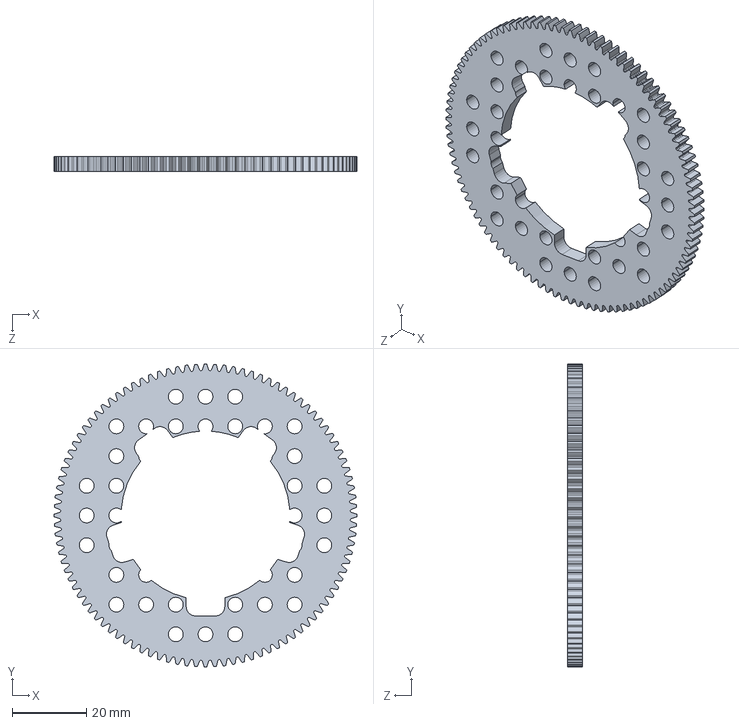
[picture p77: CAD file, 2024-04-28]
CAD/knob engagement, motorized rotation, passive translation/small knob shell 2.SLDPRT
81.6 x 81.6 x 4.00 mm
