ns8483/MAE156A_RobotAssistantCardiologist/CAD/Probe and Housing/big_knob.SLDPRT

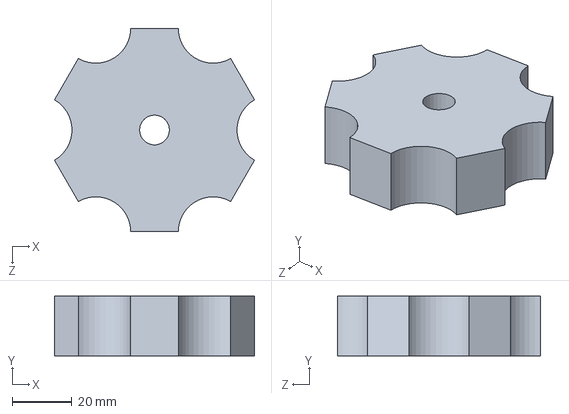
[picture p78: CAD file, 2024-04-26]
CAD/Probe and Housing/big_knob.SLDPRT
67.0 x 20.0 x 68.2 mm
