ns8483/MAE156A_RobotAssistantCardiologist/CAD/knob engagement, motorized rotation, passive translation/bottom acrylic w servo mountingSLDPRT.SLDPRT

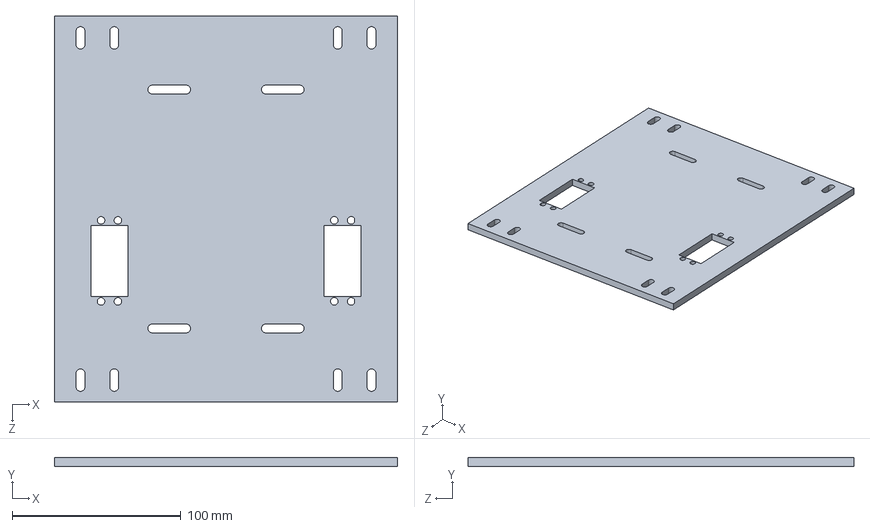
[picture p79: CAD file, 2024-04-28]
CAD/knob engagement, motorized rotation, passive translation/bottom acrylic w servo mountingSLDPRT.SLDPRT
203.2 x 5.59 x 228.6 mm
