ns8483/MAE156A_RobotAssistantCardiologist/CAD/Probe and Housing/Dial Large.SLDPRT

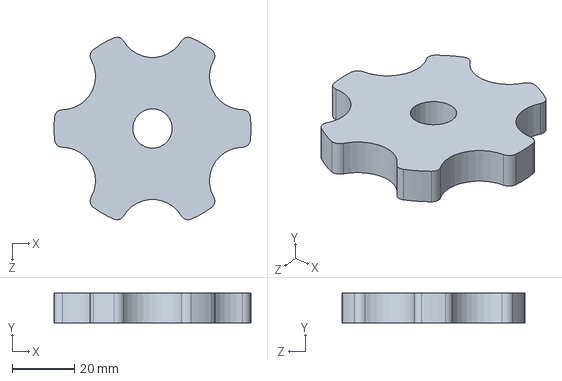
[picture p80: CAD file, 2024-04-26]
CAD/Probe and Housing/Dial Large.SLDPRT
63.4 x 9.65 x 58.8 mm
