ns8483/MAE156A_RobotAssistantCardiologist/CAD/Attachement/Ball Bearing_25ID_37OD.SLDPRT

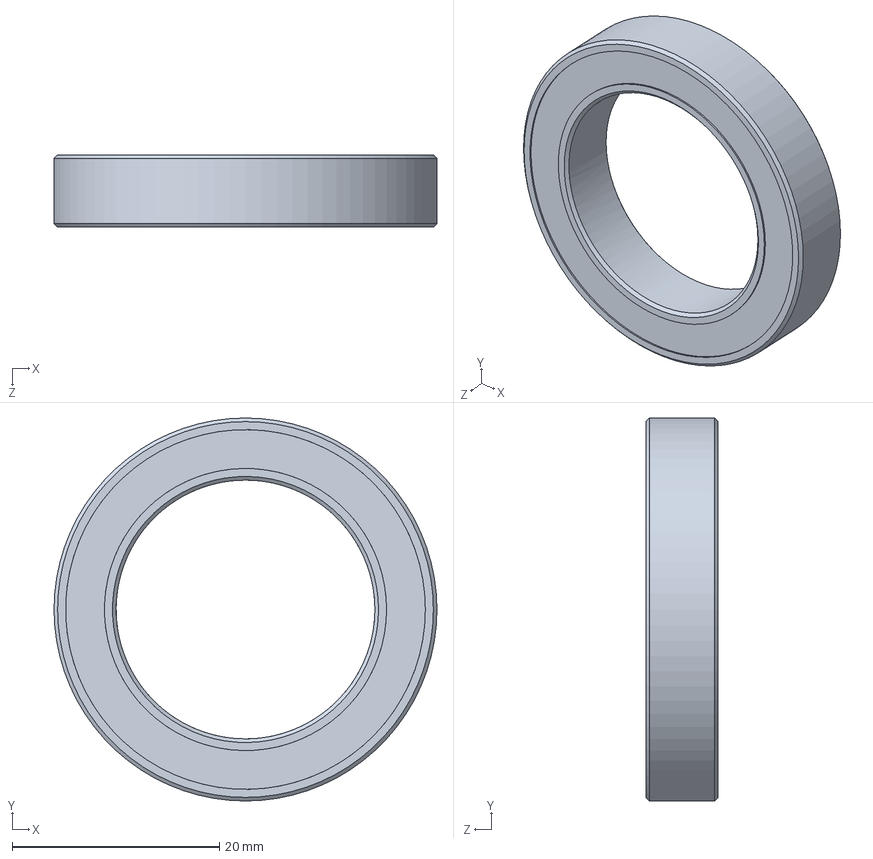
[picture p81: CAD file, 2024-04-26]
CAD/Attachement/Ball Bearing_25ID_37OD.SLDPRT
37.0 x 37.0 x 7.00 mm
