ns8483/MAE156A_RobotAssistantCardiologist/CAD/Base/Hinge Lid.SLDPRT

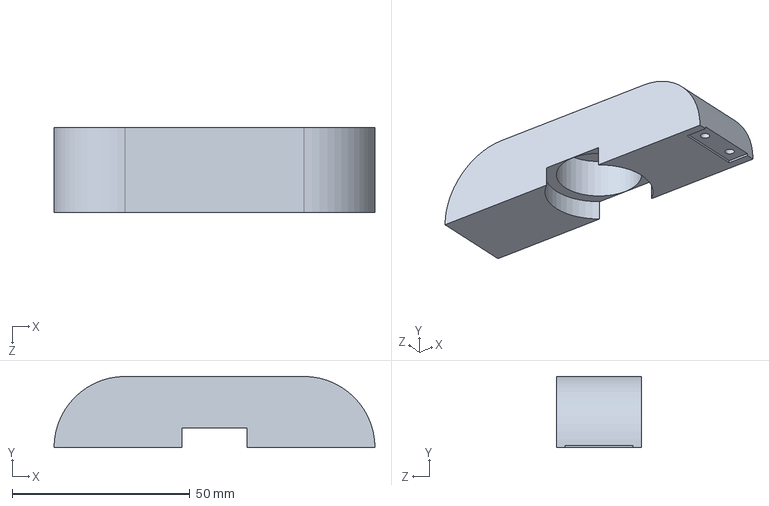
[picture p83: CAD file, 2024-04-26]
CAD/Base/Hinge Lid.SLDPRT
90.2 x 20.0 x 24.0 mm
