ns8483/MAE156A_RobotAssistantCardiologist/CAD/knob engagement, motorized rotation, passive translation/middle top acrylic.SLDPRT

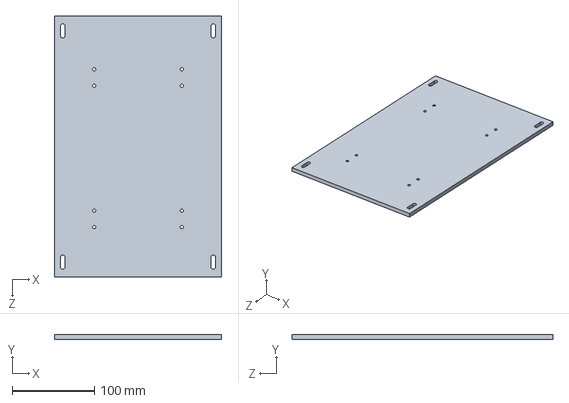
[picture p84: CAD file, 2024-04-28]
CAD/knob engagement, motorized rotation, passive translation/middle top acrylic.SLDPRT
203.2 x 5.59 x 317.5 mm
