ns8483/MAE156A_RobotAssistantCardiologist/CAD/Probe and Housing/dummy pulley.SLDPRT

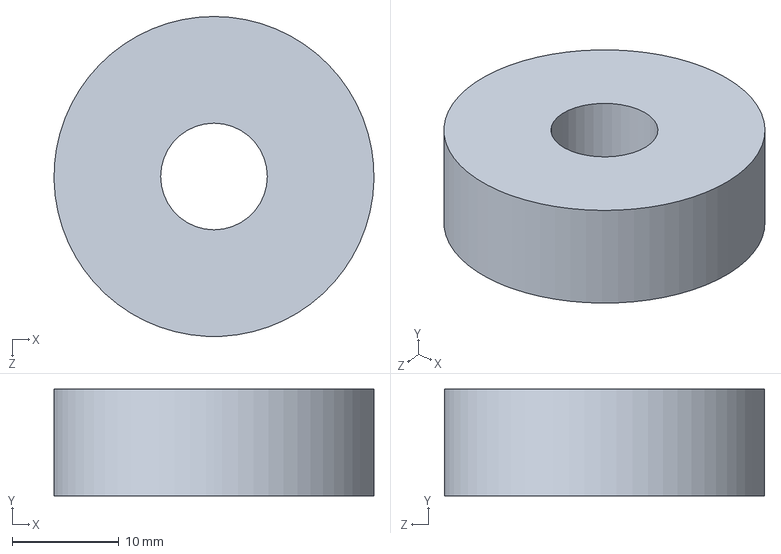
[picture p85: CAD file, 2024-04-26]
CAD/Probe and Housing/dummy pulley.SLDPRT
30.0 x 10.0 x 30.0 mm
