ns8483/MAE156A_RobotAssistantCardiologist/CAD/Attachement/FA-PL100-12-100.step

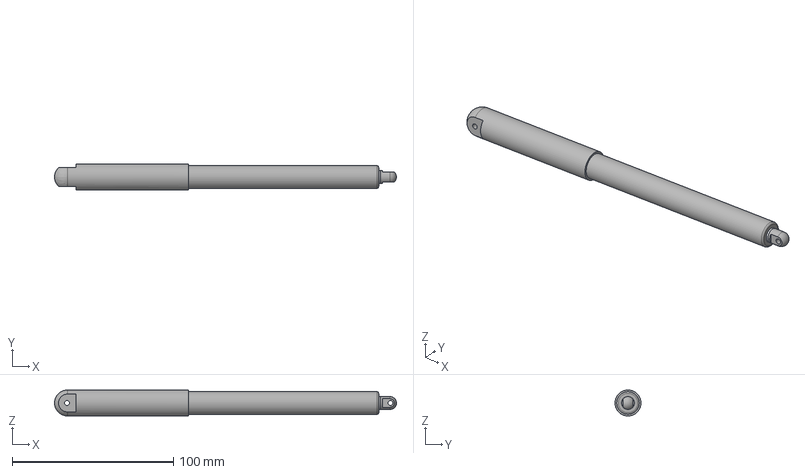
[picture p86: CAD file, 2024-04-26]
CAD/Attachement/FA-PL100-12-100.step
212.0 x 16.1 x 16.1 mm
Cylinder Body
Cylinder Rod
Cylinder End Rod
