ns8483/MAE156A_RobotAssistantCardiologist/CAD/Base/Trans Adapter.SLDPRT

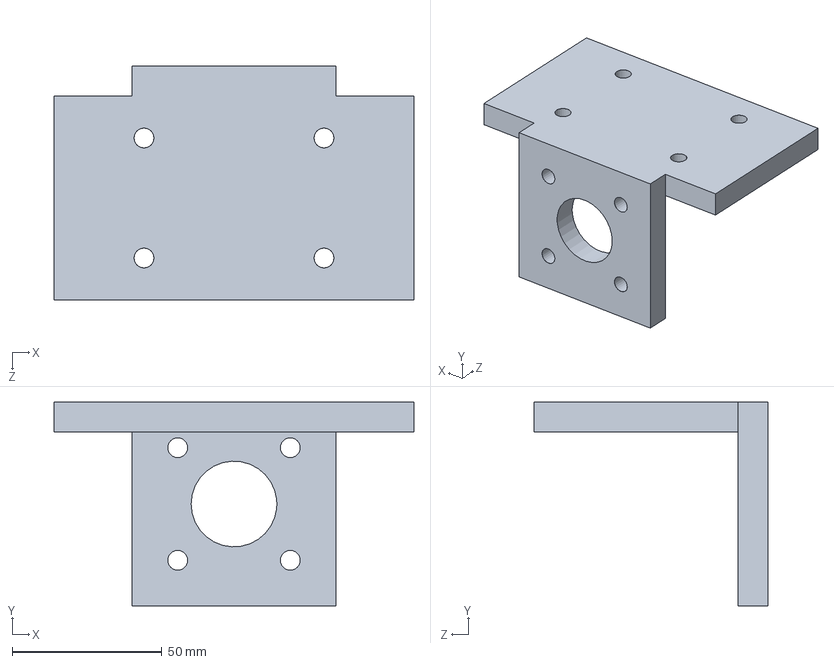
[picture p87: CAD file, 2024-04-26]
CAD/Base/Trans Adapter.SLDPRT
120.0 x 68.0 x 78.0 mm
