ns8483/MAE156A_RobotAssistantCardiologist/CAD/knob engagement, motorized rotation, passive translation/outside end acrylic.SLDPRT

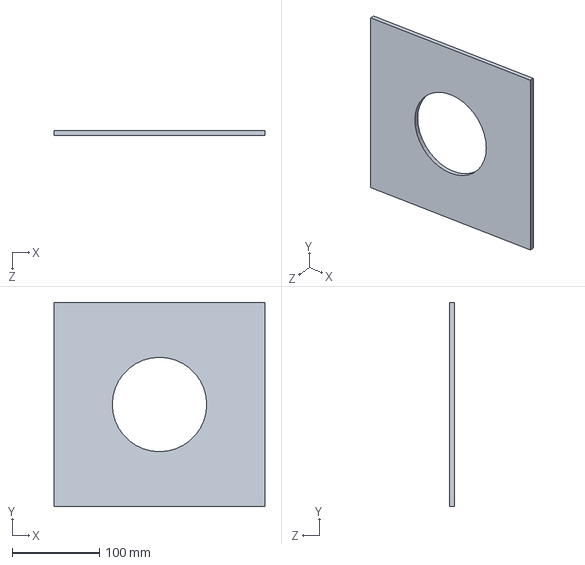
[picture p88: CAD file, 2024-04-28]
CAD/knob engagement, motorized rotation, passive translation/outside end acrylic.SLDPRT
241.3 x 233.4 x 5.59 mm
