ns8483/MAE156A_RobotAssistantCardiologist/CAD/Probe and Housing/dummy release button.SLDPRT

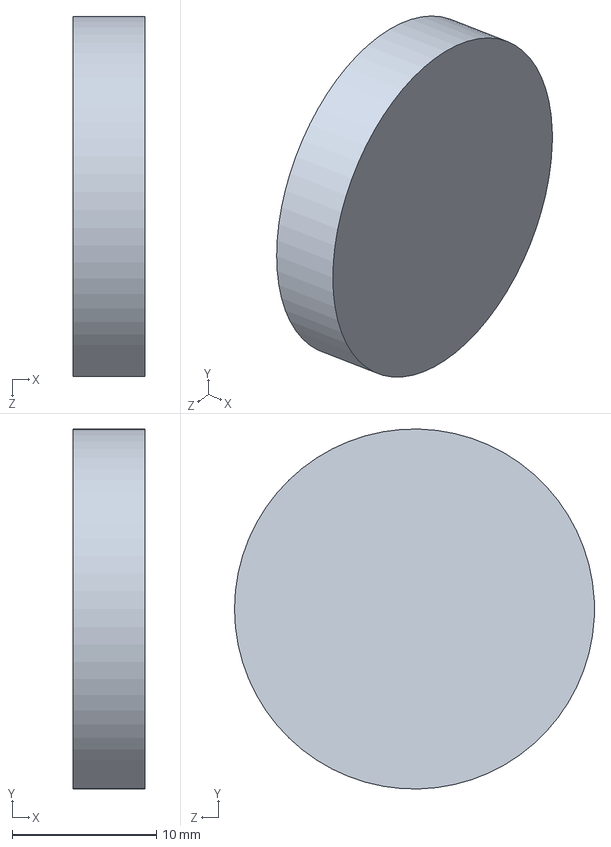
[picture p89: CAD file, 2024-04-26]
CAD/Probe and Housing/dummy release button.SLDPRT
5.00 x 25.0 x 25.0 mm
