ns8483/MAE156A_RobotAssistantCardiologist/CAD/Attachement/Rotator Pin.SLDPRT

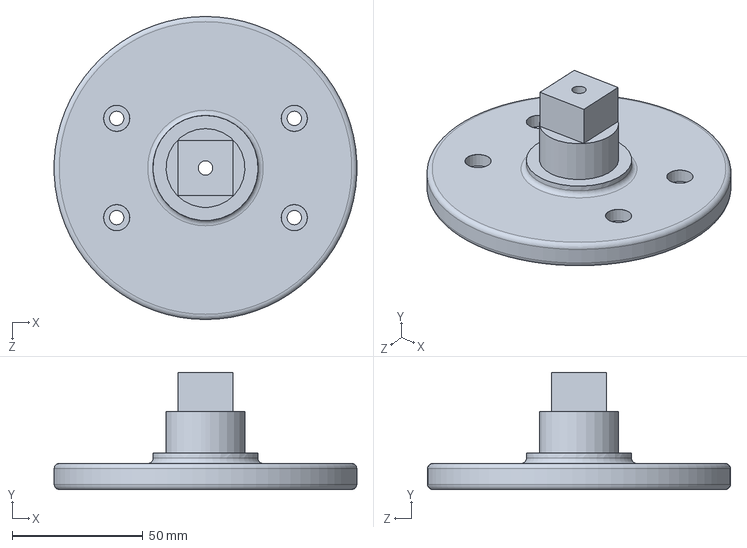
[picture p90: CAD file, 2024-04-26]
CAD/Attachement/Rotator Pin.SLDPRT
115.9 x 44.8 x 116.0 mm
