ns8483/MAE156A_RobotAssistantCardiologist/CAD/Base/Catheter Guide.SLDPRT

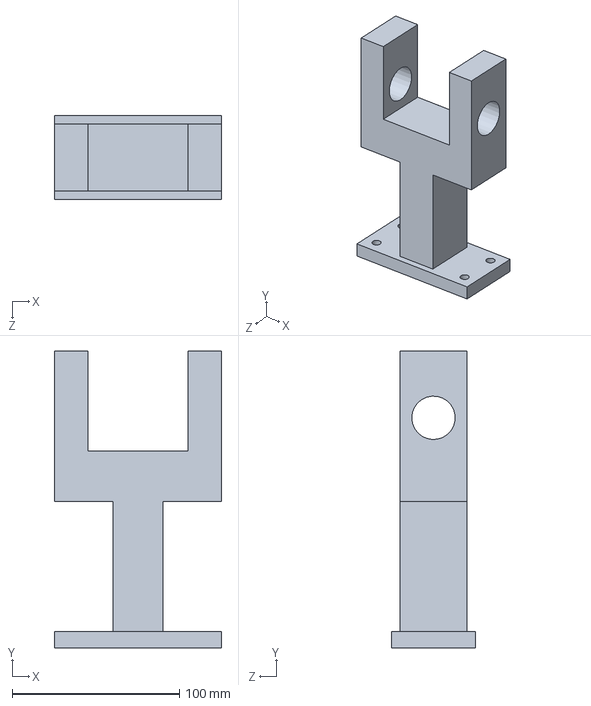
[picture p91: CAD file, 2024-04-26]
CAD/Base/Catheter Guide.SLDPRT
100.0 x 177.8 x 50.0 mm
