ns8483/MAE156A_RobotAssistantCardiologist/CAD/knob engagement, motorized rotation, passive translation/bottomclamp v2.step

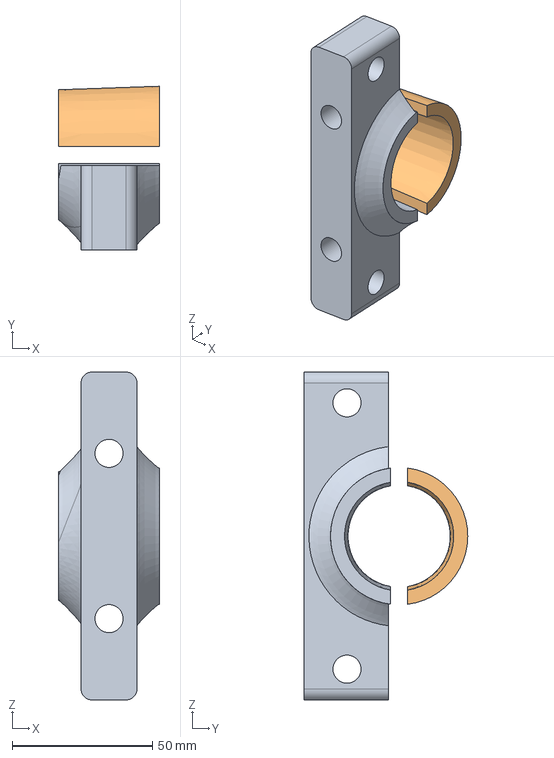
[picture p92: CAD file, 2024-04-28]
CAD/knob engagement, motorized rotation, passive translation/bottomclamp v2.step
36.0 x 58.3 x 116.9 mm
