ns8483/MAE156A_RobotAssistantCardiologist/CAD/knob engagement, motorized rotation, passive translation/corner bracket.SLDPRT

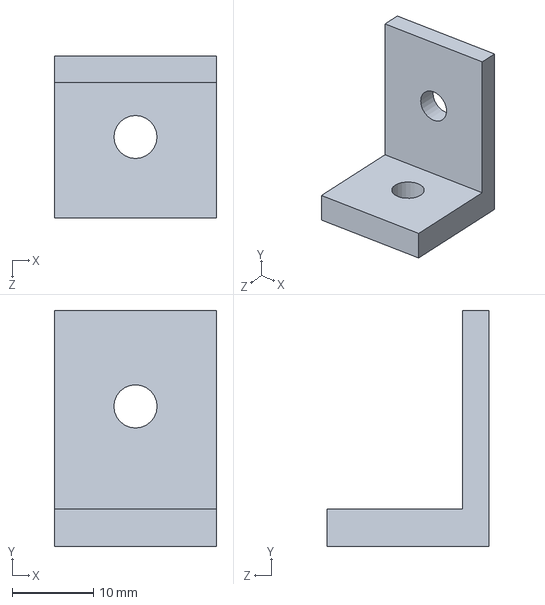
[picture p93: CAD file, 2024-04-28]
CAD/knob engagement, motorized rotation, passive translation/corner bracket.SLDPRT
20.0 x 29.1 x 20.0 mm
