ns8483/MAE156A_RobotAssistantCardiologist/CAD/Attachement/0.5in Side Ball Bearing.SLDPRT

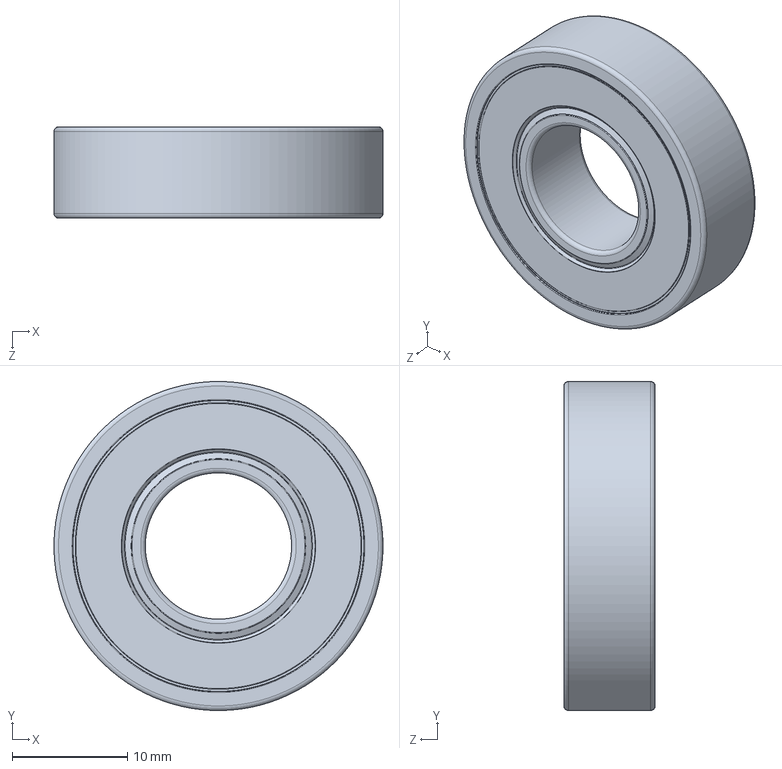
[picture p94: CAD file, 2024-04-26]
CAD/Attachement/0.5in Side Ball Bearing.SLDPRT
28.6 x 28.6 x 7.94 mm
