ns8483/MAE156A_RobotAssistantCardiologist/CAD/Attachement/Attachment.SLDPRT

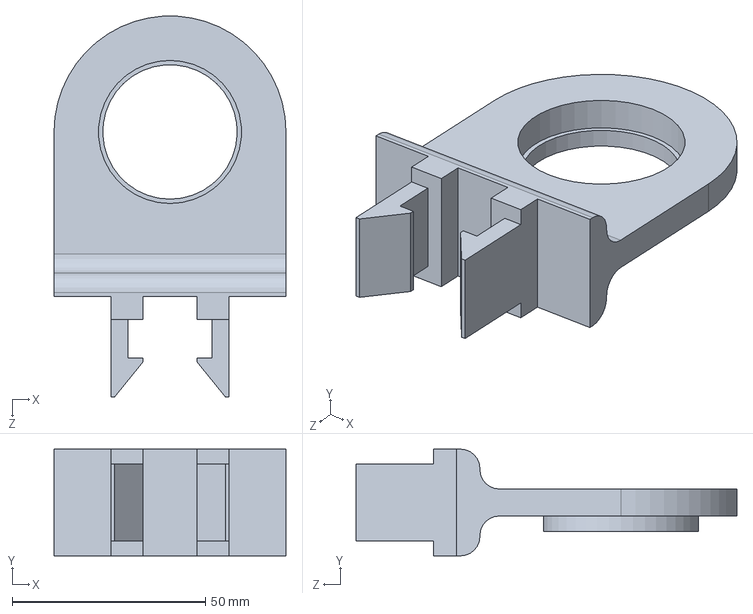
[picture p95: CAD file, 2024-04-26]
CAD/Attachement/Attachment.SLDPRT
60.0 x 27.6 x 98.4 mm
