ns8483/MAE156A_RobotAssistantCardiologist/CAD/knob engagement, motorized rotation, passive translation/middle end acrylic.SLDPRT

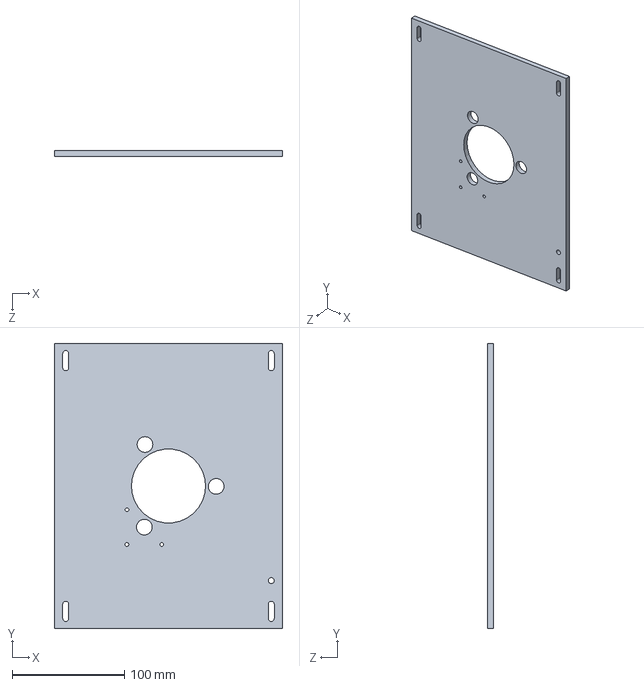
[picture p96: CAD file, 2024-04-28]
CAD/knob engagement, motorized rotation, passive translation/middle end acrylic.SLDPRT
203.2 x 254.0 x 5.59 mm
