ns8483/MAE156A_RobotAssistantCardiologist/CAD/Attachement/Rotator Cap.SLDPRT

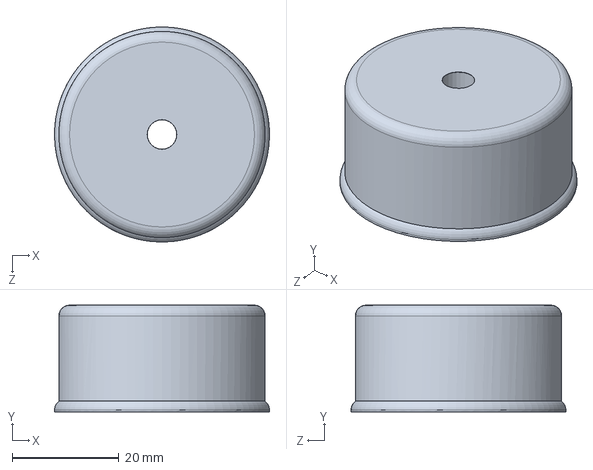
[picture p97: CAD file, 2024-04-26]
CAD/Attachement/Rotator Cap.SLDPRT
40.2 x 20.0 x 40.2 mm
