ns8483/MAE156A_RobotAssistantCardiologist/CAD/knob engagement, motorized rotation, passive translation/2301-0006-0015.step

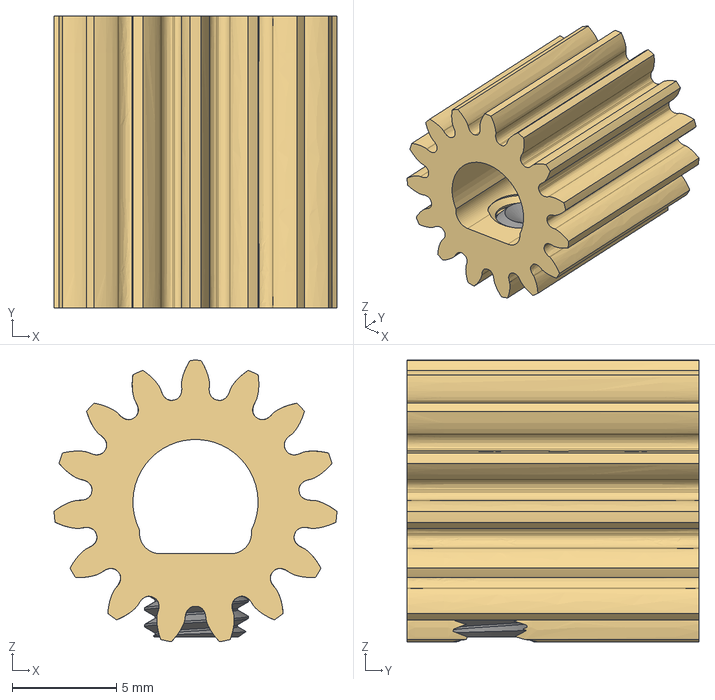
[picture p98: CAD file, 2024-04-28]
CAD/knob engagement, motorized rotation, passive translation/2301-0006-0015.step
13.6 x 14.0 x 13.5 mm
2301-0006-0015 without hardware
