ns8483/MAE156A_RobotAssistantCardiologist/CAD/Attachement/Base Plate.SLDPRT

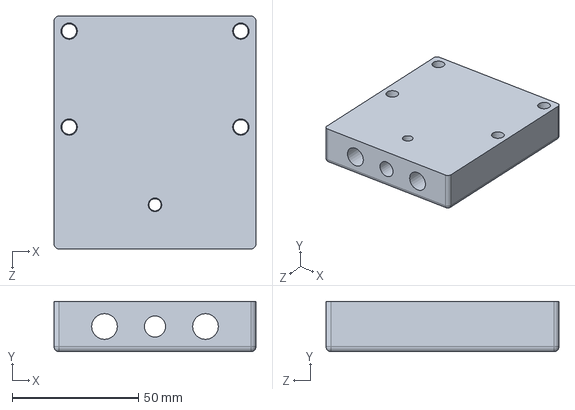
[picture p99: CAD file, 2024-04-26]
CAD/Attachement/Base Plate.SLDPRT
80.0 x 20.0 x 92.3 mm
