ns8483/MAE156A_RobotAssistantCardiologist/CAD/knob engagement, motorized rotation, passive translation/MG995.STEP

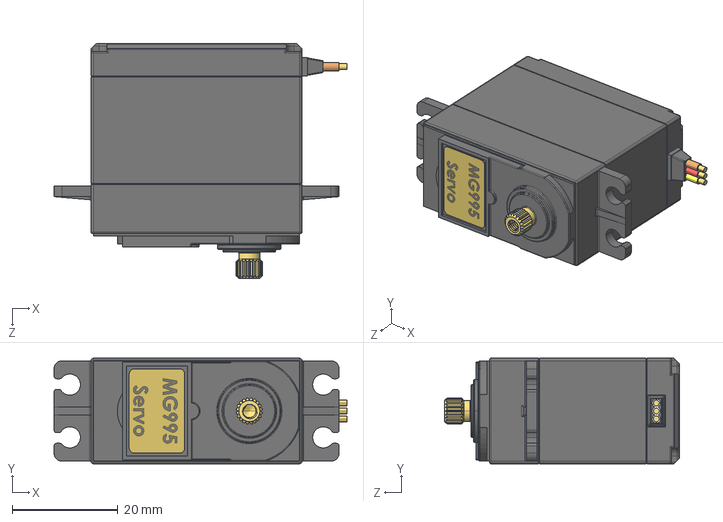
[picture p100: CAD file, 2024-04-28]
CAD/knob engagement, motorized rotation, passive translation/MG995.STEP
55.5 x 20.0 x 44.5 mm
