ns8483/MAE156A_RobotAssistantCardiologist/CAD/knob engagement, motorized rotation, passive translation/outside side acrylic.SLDPRT

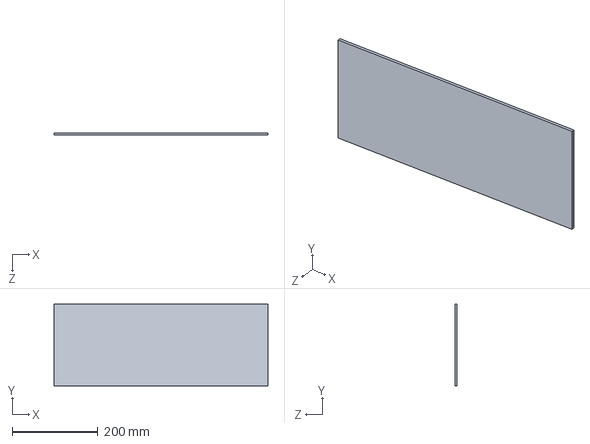
[picture p101: CAD file, 2024-04-28]
CAD/knob engagement, motorized rotation, passive translation/outside side acrylic.SLDPRT
500.0 x 190.5 x 5.59 mm
