ns8483/MAE156A_RobotAssistantCardiologist/CAD/Attachement/Worm Shaft.SLDPRT

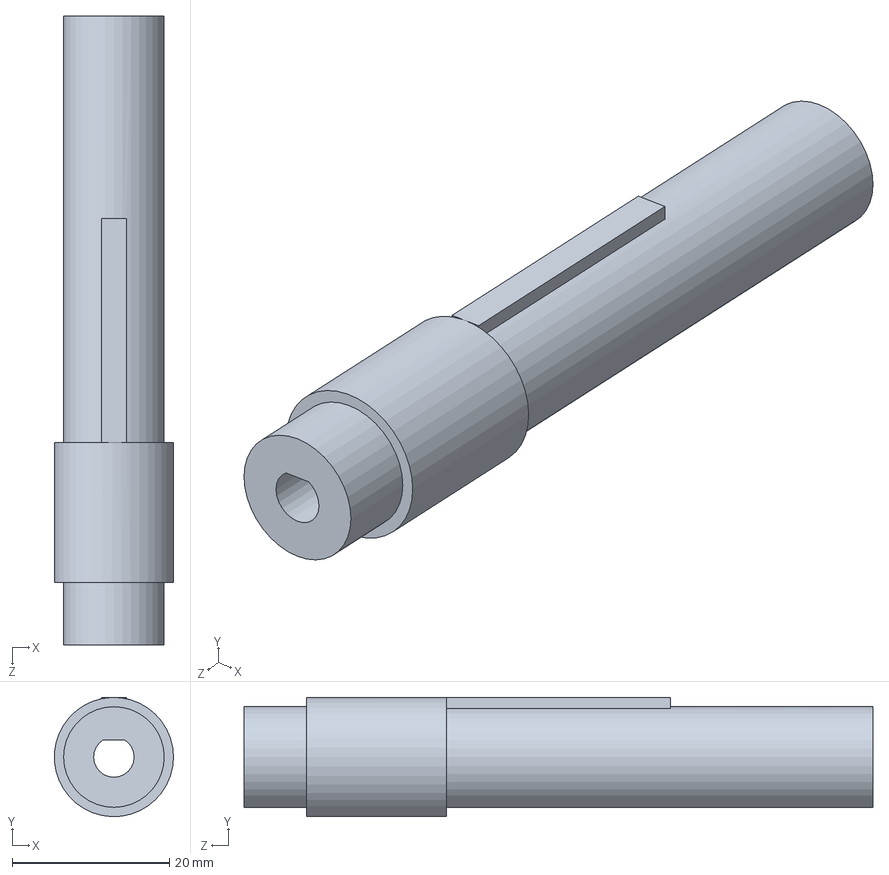
[picture p102: CAD file, 2024-04-26]
CAD/Attachement/Worm Shaft.SLDPRT
15.1 x 15.2 x 80.0 mm
