ns8483/MAE156A_RobotAssistantCardiologist/CAD/knob engagement, motorized rotation, passive translation/outside bottom acrylic.SLDPRT

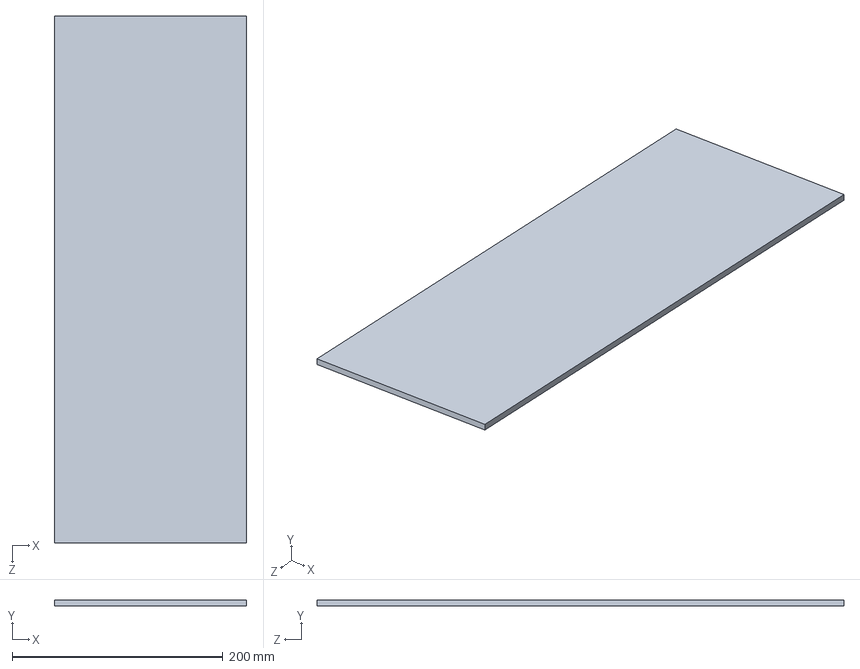
[picture p103: CAD file, 2024-04-28]
CAD/knob engagement, motorized rotation, passive translation/outside bottom acrylic.SLDPRT
182.6 x 5.59 x 500.0 mm
