ns8483/MAE156A_RobotAssistantCardiologist/CAD/Attachement/Clamp.SLDPRT

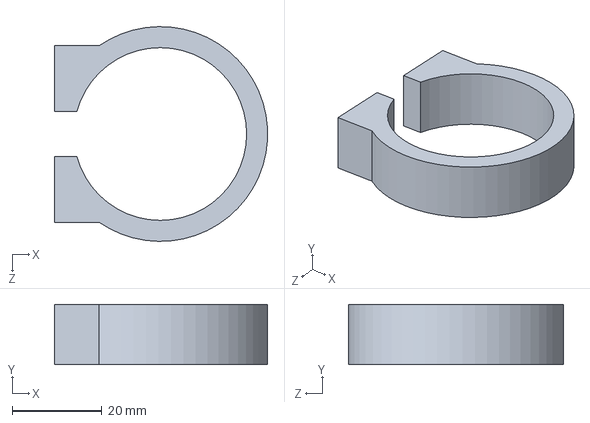
[picture p104: CAD file, 2024-04-26]
CAD/Attachement/Clamp.SLDPRT
47.6 x 13.5 x 48.0 mm
