ns8483/MAE156A_RobotAssistantCardiologist/CAD/Attachement/Nema 17 Stepper Motor.SLDPRT

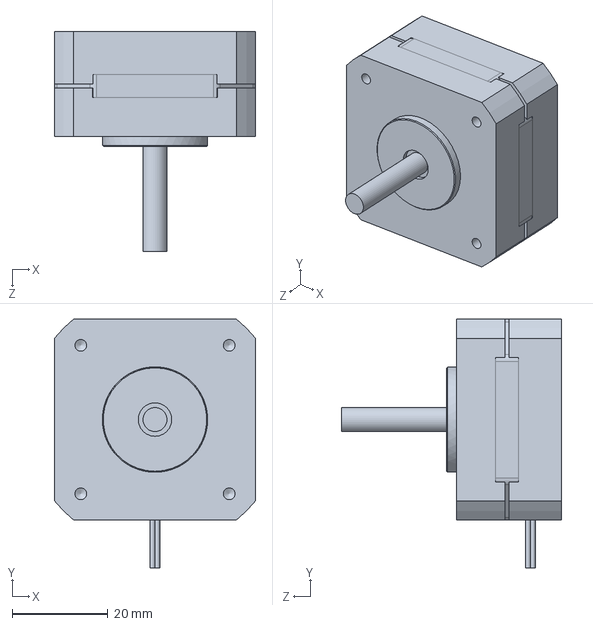
[picture p105: CAD file, 2024-04-26]
CAD/Attachement/Nema 17 Stepper Motor.SLDPRT
42.0 x 52.0 x 46.0 mm
