ns8483/MAE156A_RobotAssistantCardiologist/CAD/knob engagement, motorized rotation, passive translation/coupler.SLDPRT

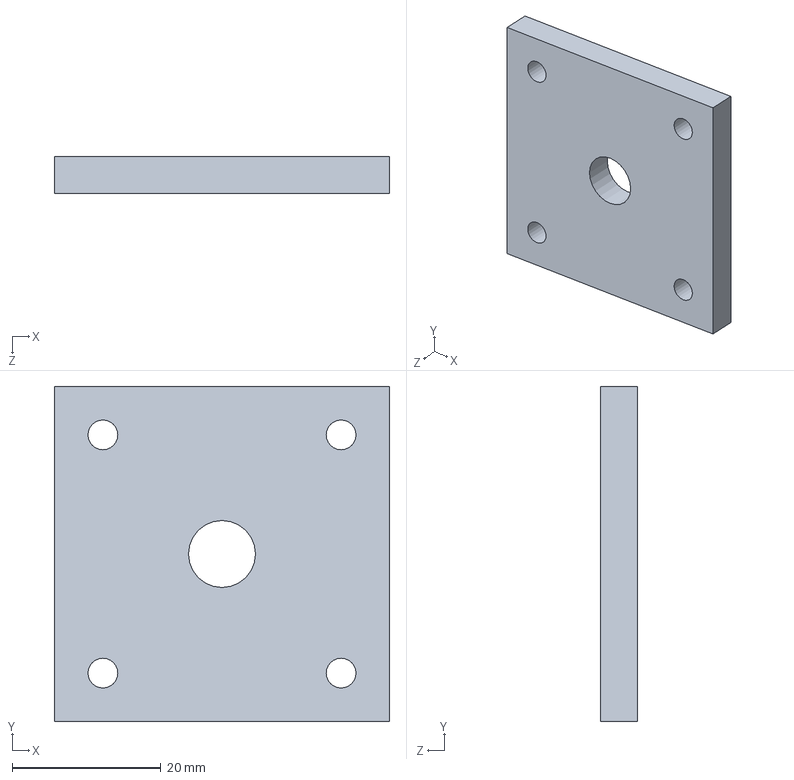
[picture p106: CAD file, 2024-04-28]
CAD/knob engagement, motorized rotation, passive translation/coupler.SLDPRT
45.0 x 45.0 x 5.00 mm
