ns8483/MAE156A_RobotAssistantCardiologist/CAD/knob engagement, motorized rotation, passive translation/top acrylic.SLDPRT

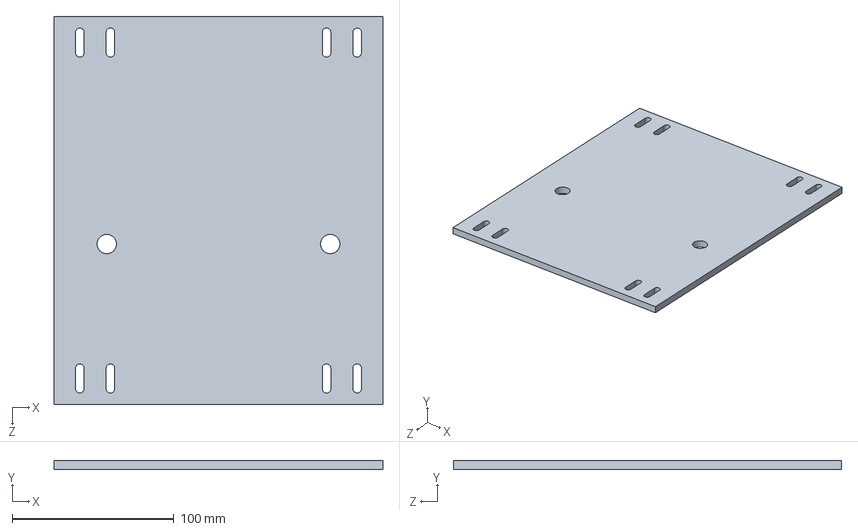
[picture p107: CAD file, 2024-04-28]
CAD/knob engagement, motorized rotation, passive translation/top acrylic.SLDPRT
203.2 x 5.59 x 239.8 mm
