ns8483/MAE156A_RobotAssistantCardiologist/CAD/knob engagement, motorized rotation, passive translation/2101-0006-0120.STEP

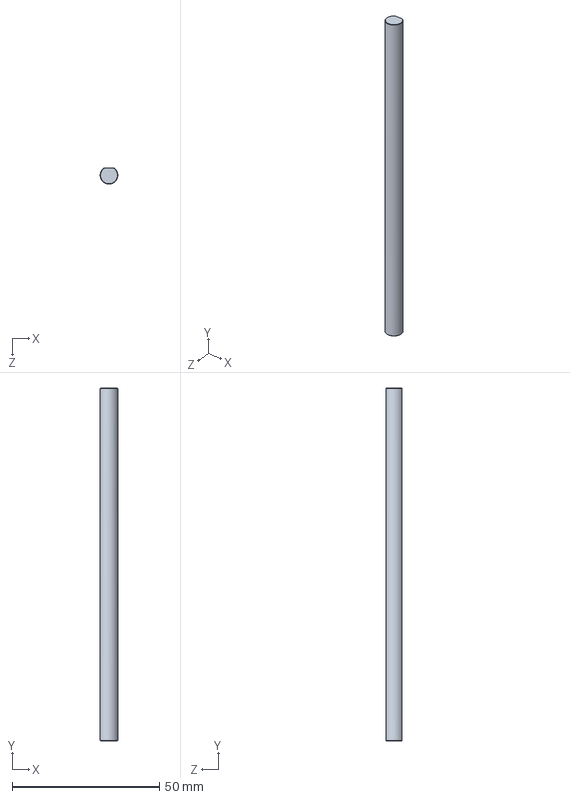
[picture p108: CAD file, 2024-04-28]
CAD/knob engagement, motorized rotation, passive translation/2101-0006-0120.STEP
6.00 x 120.0 x 5.50 mm
