ns8483/MAE156A_RobotAssistantCardiologist/CAD/knob engagement, motorized rotation, passive translation/Dial Small.SLDPRT

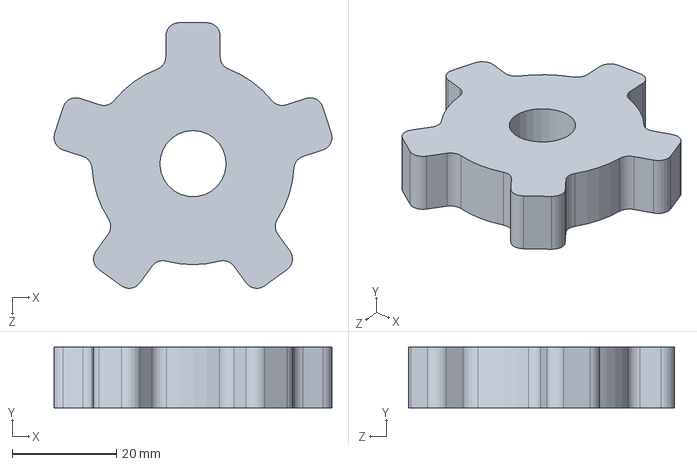
[picture p109: CAD file, 2024-04-26]
CAD/knob engagement, motorized rotation, passive translation/Dial Small.SLDPRT
53.3 x 11.7 x 51.0 mm
