ns8483/MAE156A_RobotAssistantCardiologist/CAD/Attachement/Micro Linear Actuator 100mm.SLDASM

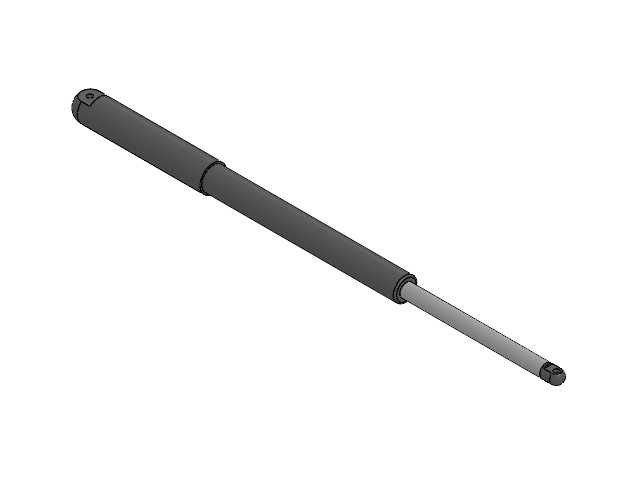
[picture p115: CAD file, 2024-04-26]
CAD/Attachement/Micro Linear Actuator 100mm.SLDASM
Cylinder Body
Cylinder Rod
Cylinder End Rod
