ns8483/MAE156A_RobotAssistantCardiologist/CAD/Attachement/Square Lock Assembly.SLDASM

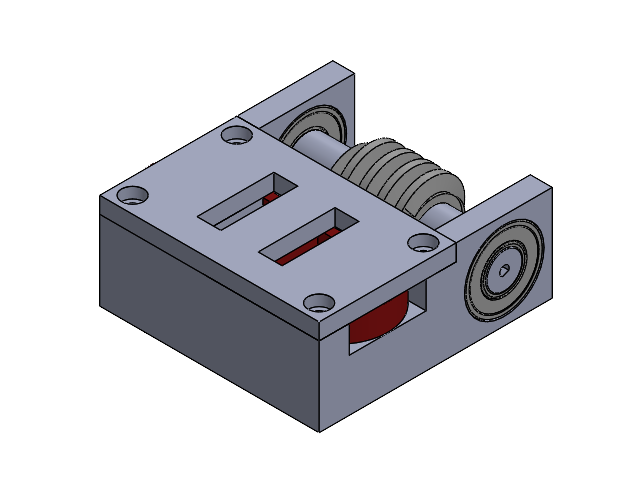
[picture p116: CAD file, 2024-04-26]
CAD/Attachement/Square Lock Assembly.SLDASM
square lock base
Square Lock pin x 2
Square Lid
0.5in Side Ball Bearing x 2
Worm Shaft
57545K527_Metal Worm
Shaft Adapter
