ns8483/MAE156A_RobotAssistantCardiologist/CAD/knob engagement, motorized rotation, passive translation/4002-0005-0006 assembly.SLDASM

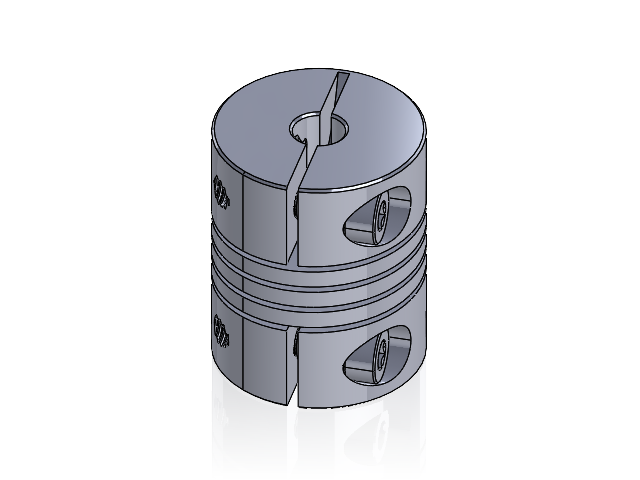
[picture p117: CAD file, 2024-04-28]
CAD/knob engagement, motorized rotation, passive translation/4002-0005-0006 assembly.SLDASM
4002-0005-0006.STEP
4002 series set-screw_91390A112.STEP x 2
4002 series pinch bolt_91290A115.STEP x 2
