ns8483/MAE156A_RobotAssistantCardiologist/Firmware/Xbox Servo Test/servoController.pde

import processing.serial.*;

import net.java.games.input.*;
import org.gamecontrolplus.*;
import org.gamecontrolplus.gui.*;

import cc.arduino.*;
import org.firmata.*;

ControlDevice cont;
ControlIO control;

Arduino arduino;

float thumb;

void setup() {
  size(360, 200);
  
  control = ControlIO.getInstance(this);
  cont = control.getMatchedDevice("xbs");
  
  if (cont == null){
    print("not todday chump");
    System.exit(-1);
  }
  
  //println(Arduino.list());
  arduino = new Arduino(this, Arduino.list()[2], 57600);
  arduino.pinMode(10, Arduino.SERVO);
}

public void getUserInput(){
  //assign our float value
  //access the controller
  thumb = map(cont.getSlider("servo").getValue(),-1, 1, 0, 180);
  //println(thumb);
}

void draw() {
  getUserInput();
  background(thumb,100,255);
  
  arduino.servoWrite(10, (int)thumb);
}
  
