ns8483/MAE156A_RobotAssistantCardiologist/Firmware/Radio Testing/RF_Receiver.ino

#include <SPI.h>
#include <nRF24L01.h>
#include <RF24.h>

int CE_PIN = 9;
int CSN_PIN = 10;

RF24 radio(CE_PIN,CSN_PIN);
const byte address[6] = "00001";

void setup() {
  Serial.begin(4800);
  radio.begin();
  radio.openReadingPipe(1, address);
  radio.setPALevel(RF24_PA_MIN);
  radio.startListening();
}

void loop() {
  Serial.println("fail");
  if (radio.available()) {
    char text[32] = "";
    radio.read(&text, sizeof(text));
    delay(5);
    Serial.println(text);
  }
  delay(200);
}
